666zhaobo666/HoloCubic/源码/My_AIO_Firmware_PIO/src/app/game_2048/README.md

### 2048游戏
APP由`AndyXFuture`编写，原项目链接为`https://github.com/AndyXFuture/HoloCubic-2048-anim`
