666zhaobo666/HoloCubic/源码/My_AIO_Firmware_PIO/src/app/game_snake/README.md

### Snake贪吃蛇
APP由`niyongsheng`编写，项目链接为`https://github.com/niyongsheng/HoloCubic`
