666zhaobo666/HoloCubic/源码/My_AIO_Firmware_PIO/src/app/tomato/README.md

# HoloCubic_AIO_Tomato_Clock_V2.0
透明小电视番茄时钟2.0

本项目基于的代码 https://github.com/ClimbSnail/HoloCubic_AIO
# 原作者
kylefjl

原项目链接：https://github.com/kylefjl/HoloCubic_AIO_TOMATO
# 更新内容
# 界面类

1、增加“专注/休息中.....”运行动画

2、增加毛玻璃效果

# 功能类

1、新增添2个档位：专注45分钟，休息15分钟

2、实现可调节倒计时时间：
  在倒计时进行时，保持前倾增加倒计时开始时间，前倾一下重置当前已设置的倒计时时间
  
# 其他类

1、将倒计时结束时单色闪烁改为RGB渐变闪烁
