666zhaobo666/HoloCubic/AIO_Tool/Holo.png

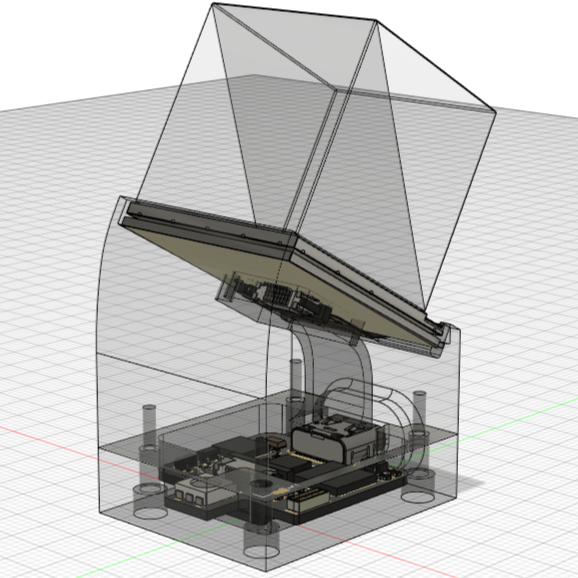
AIO_Tool/Holo.png
