666zhaobo666/HoloCubic/Image/app_bilibili.png

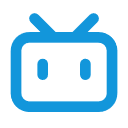
Image/app_bilibili.png
