666zhaobo666/HoloCubic/Image/app_file_manager.png

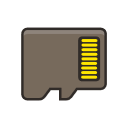
Image/app_file_manager.png
