666zhaobo666/HoloCubic/Image/app_file_maneger_1.png

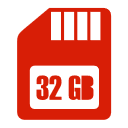
Image/app_file_maneger_1.png
