666zhaobo666/HoloCubic/Image/app_loading.png

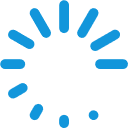
Image/app_loading.png
