666zhaobo666/HoloCubic/Image/app_movie2.png

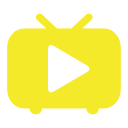
Image/app_movie2.png
