666zhaobo666/HoloCubic/Image/app_movie.png

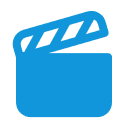
Image/app_movie.png
