666zhaobo666/HoloCubic/Image/app_remote sensor.png

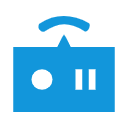
Image/app_remote sensor.png
