666zhaobo666/HoloCubic/Image/app_screen.png

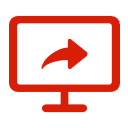
Image/app_screen.png
