666zhaobo666/HoloCubic/Image/app_thought.png

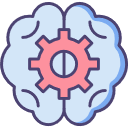
Image/app_thought.png
