666zhaobo666/HoloCubic/Image/app_weather.png

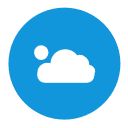
Image/app_weather.png
