666zhaobo666/HoloCubic/Image/bilibili.png

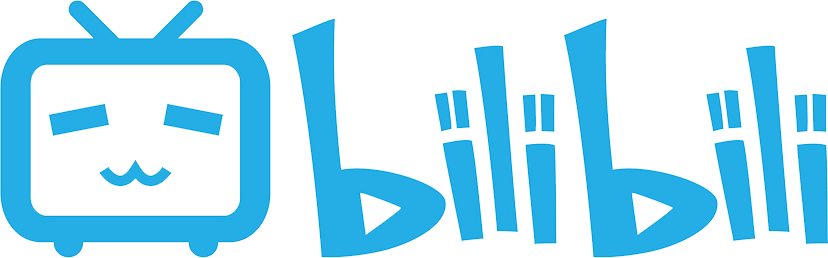
Image/bilibili.png
