666zhaobo666/HoloCubic/Image/butterfly_1.jpg

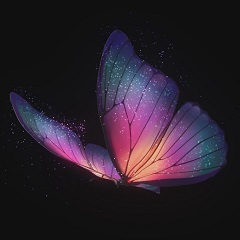
Image/butterfly_1.jpg
