666zhaobo666/HoloCubic/Image/butterfly_2.jpg

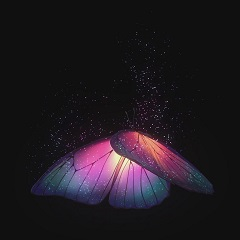
Image/butterfly_2.jpg
