666zhaobo666/HoloCubic/Image/settings.png

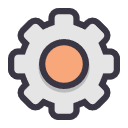
Image/settings.png
