666zhaobo666/HoloCubic/Image/settings_1.png

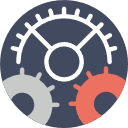
Image/settings_1.png
