666zhaobo666/HoloCubic/Image/thought_anim_2.png

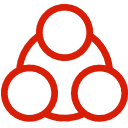
Image/thought_anim_2.png
