666zhaobo666/HoloCubic/Image/thought_anim_3.png

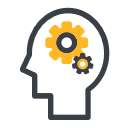
Image/thought_anim_3.png
