666zhaobo666/HoloCubic/lv_simulater_platformio/support/pio_explorer.jpg

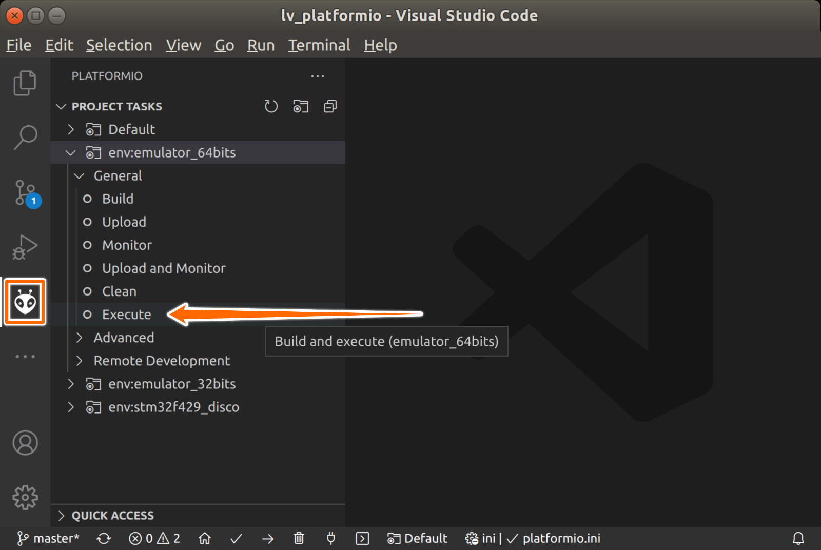
lv_simulater_platformio/support/pio_explorer.jpg
