666zhaobo666/HoloCubic/Metal简版PCB及外壳资料/3D外壳文件/Metal外壳v2.0预览图.png

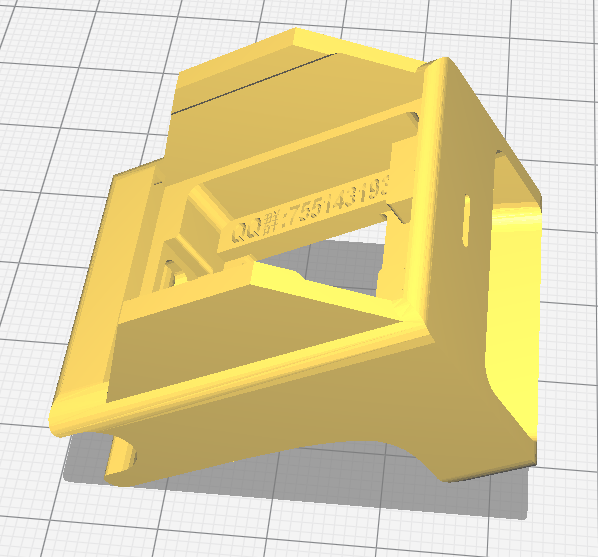
Metal简版PCB及外壳资料/3D外壳文件/Metal外壳v2.0预览图.png
