666zhaobo666/HoloCubic/Metal简版PCB及外壳资料/Metal版本说明_必看.png

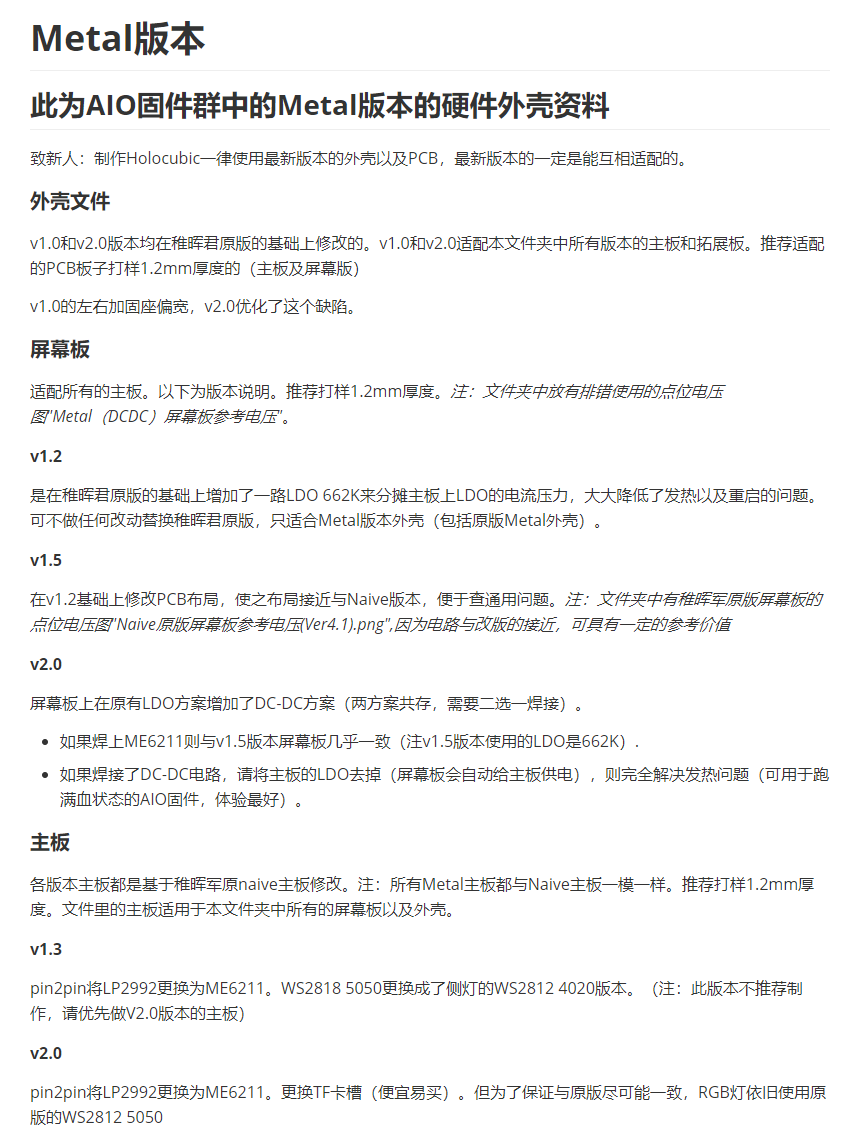
Metal简版PCB及外壳资料/Metal版本说明_必看.png
