666zhaobo666/HoloCubic/Metal简版PCB及外壳资料/主板/主板v1.3/主板v1.3渲染图.png

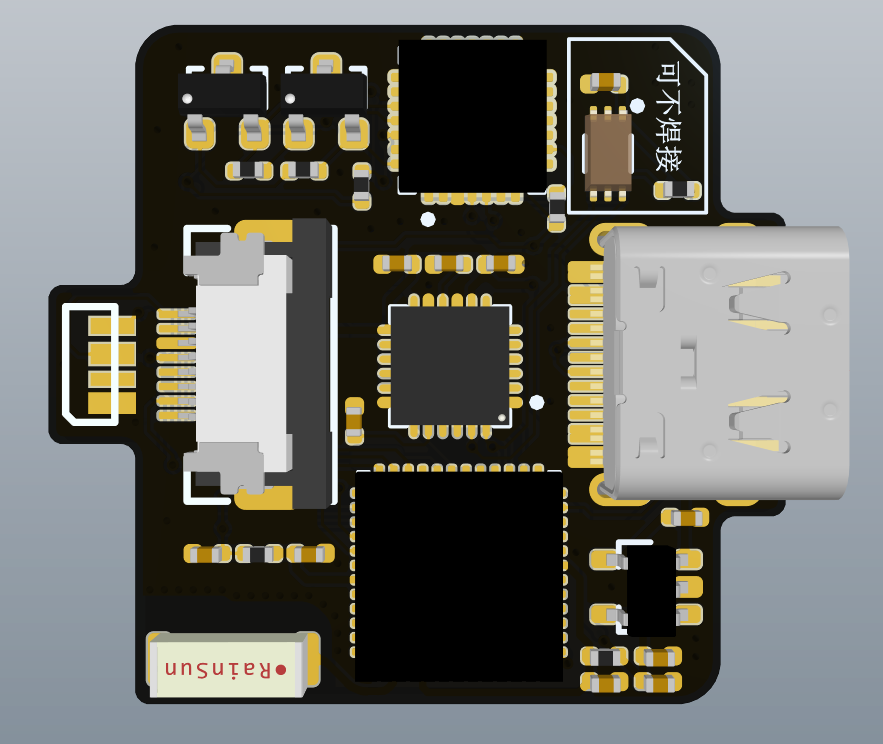
Metal简版PCB及外壳资料/主板/主板v1.3/主板v1.3渲染图.png
