666zhaobo666/HoloCubic/Metal简版PCB及外壳资料/主板/主板v2.0（原版卡槽版）/点位电压图-焊接电阻时.png

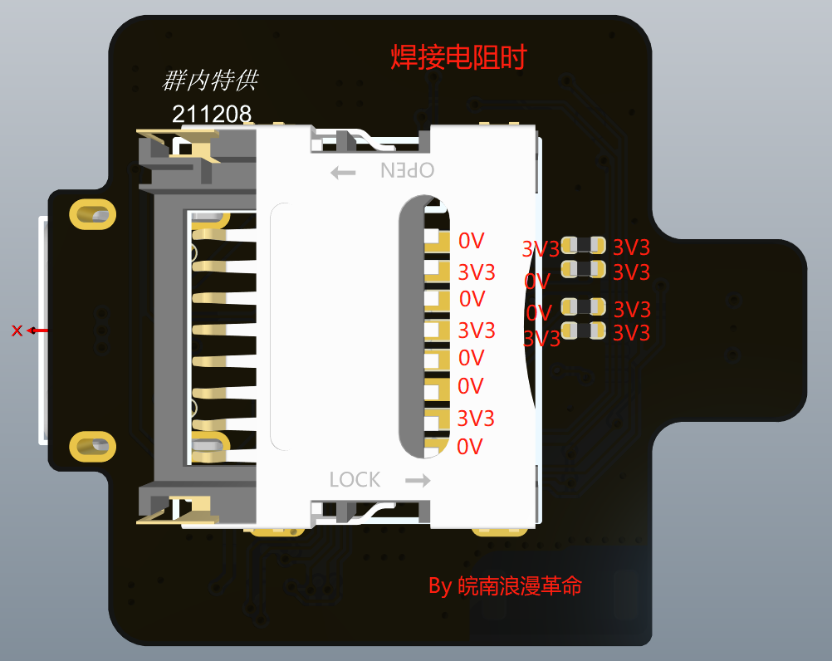
Metal简版PCB及外壳资料/主板/主板v2.0（原版卡槽版）/点位电压图-焊接电阻时.png
