666zhaobo666/HoloCubic/Metal简版PCB及外壳资料/屏幕拓展板/Metal屏幕板v2.0/Metal屏幕板v2.0渲染图.png

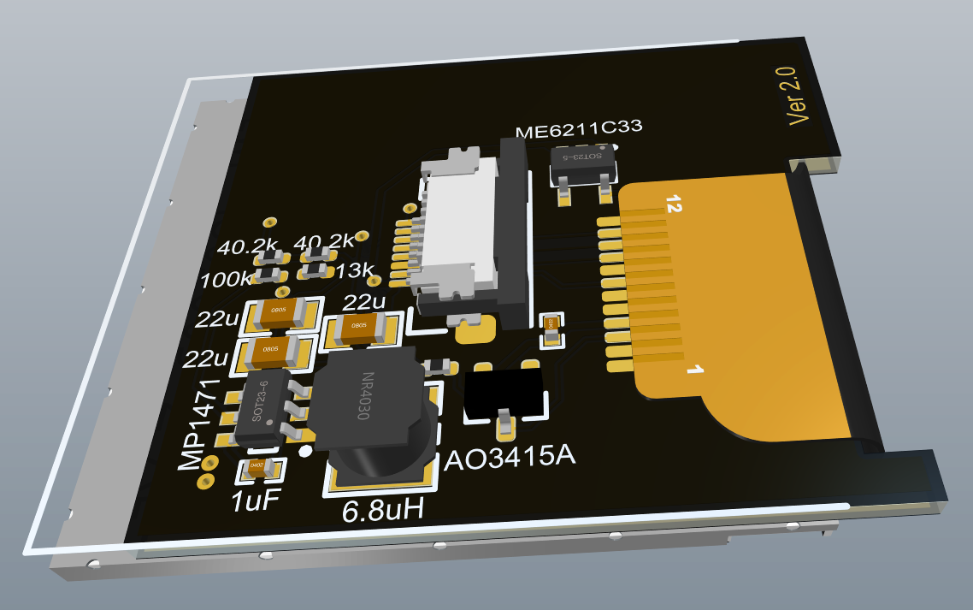
Metal简版PCB及外壳资料/屏幕拓展板/Metal屏幕板v2.0/Metal屏幕板v2.0渲染图.png
