666zhaobo666/HoloCubic/Metal简版PCB及外壳资料/屏幕拓展板/Naive原版屏幕板参考电压(Ver4.1).png

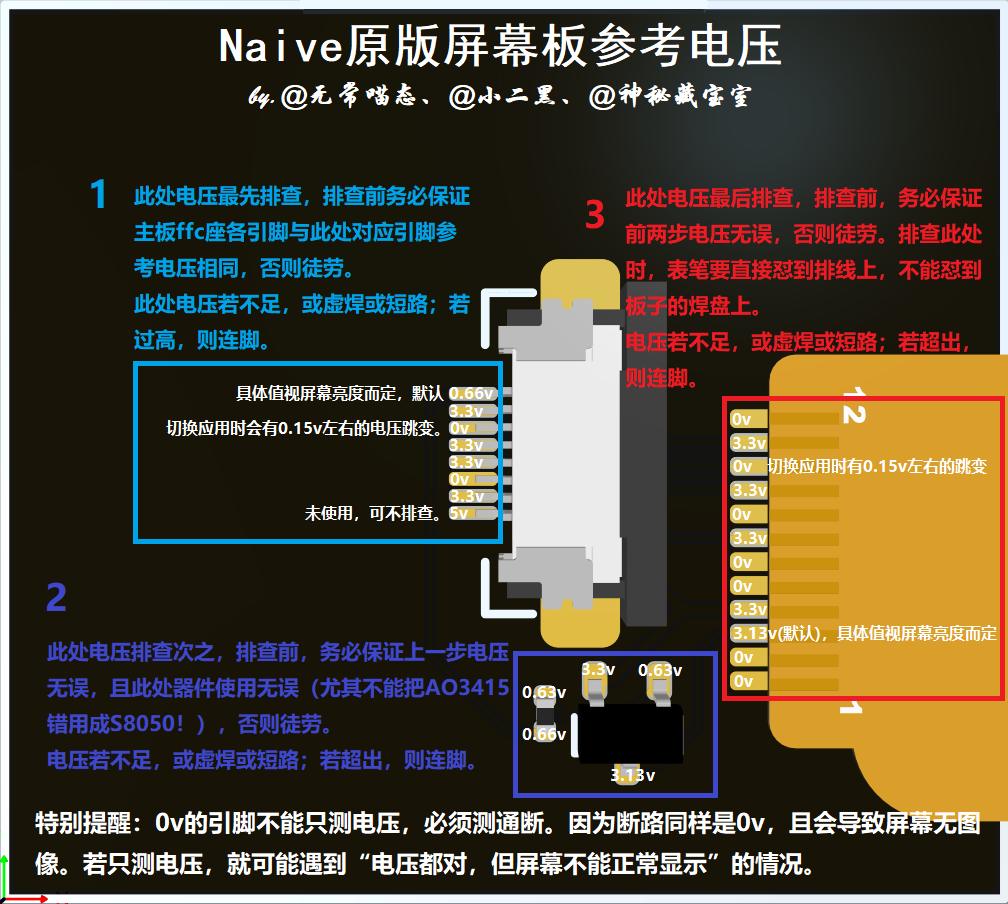
Metal简版PCB及外壳资料/屏幕拓展板/Naive原版屏幕板参考电压(Ver4.1).png
