666zhaobo666/HoloCubic/工具/专用上位机/Cubic上位机v1.4.8/放置内存卡/image/pikaqiu_2.jpg

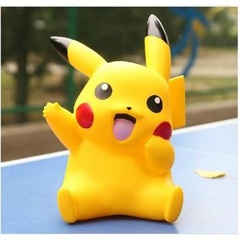
工具/专用上位机/Cubic上位机v1.4.8/放置内存卡/image/pikaqiu_2.jpg
