666zhaobo666/HoloCubic/素材/IMG_20220405_16440978.jpg

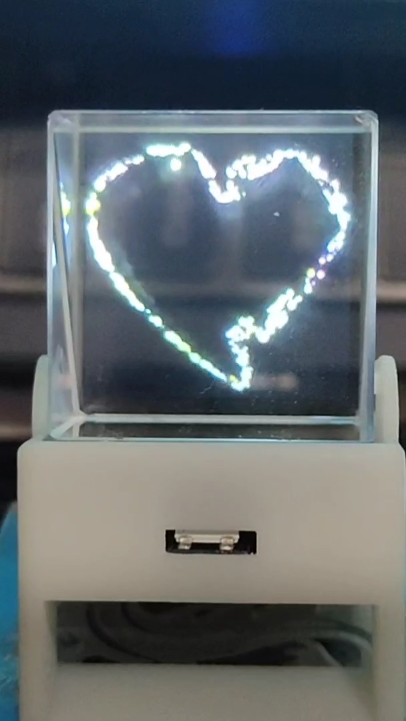
素材/IMG_20220405_16440978.jpg
