666zhaobo666/HoloCubic/素材/太空人动图.gif

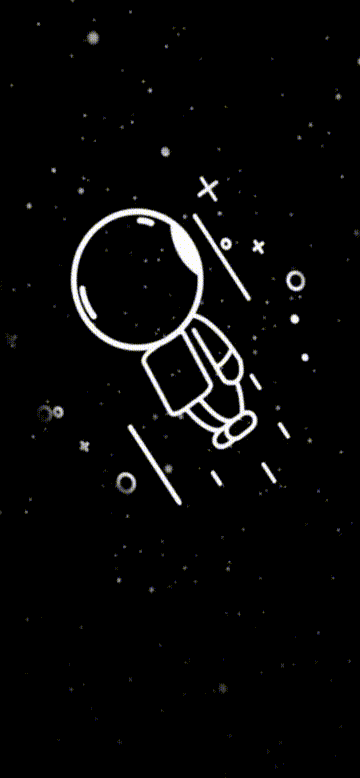
素材/太空人动图.gif
