666zhaobo666/HoloCubic/源码/HoloCubic_AIO_v2.1.8/AIO_Firmware_PIO/src/sys/app_loading.c

#include "app_controller_gui.h"

#if __has_include("lvgl.h")
#include "lvgl.h"
#else
#include "lvgl/lvgl.h"
#endif


#ifndef LV_ATTRIBUTE_MEM_ALIGN
#define LV_ATTRIBUTE_MEM_ALIGN
#endif

#ifndef LV_ATTRIBUTE_IMG_APP_LOADING
#define LV_ATTRIBUTE_IMG_APP_LOADING
#endif


const LV_ATTRIBUTE_MEM_ALIGN LV_ATTRIBUTE_LARGE_CONST LV_ATTRIBUTE_IMG_APP_LOADING uint8_t app_loading_map[] = {
  0x04, 0x02, 0x04, 0xff, 	/*Color of index 0*/
  0xdc, 0x8e, 0x14, 0xff, 	/*Color of index 1*/
  0xd4, 0x96, 0x14, 0xff, 	/*Color of index 2*/
  0xdc, 0x92, 0x14, 0xff, 	/*Color of index 3*/
  0xdc, 0x96, 0x14, 0xff, 	/*Color of index 4*/
  0xff, 0xff, 0xff, 0xff, 	/*Color of index 5*/
  0xff, 0xff, 0xff, 0xff, 	/*Color of index 6*/
  0xff, 0xff, 0xff, 0xff, 	/*Color of index 7*/
  0xff, 0xff, 0xff, 0xff, 	/*Color of index 8*/
  0xff, 0xff, 0xff, 0xff, 	/*Color of index 9*/
  0xff, 0xff, 0xff, 0xff, 	/*Color of index 10*/
  0xff, 0xff, 0xff, 0xff, 	/*Color of index 11*/
  0xff, 0xff, 0xff, 0xff, 	/*Color of index 12*/
  0xff, 0xff, 0xff, 0xff, 	/*Color of index 13*/
  0xff, 0xff, 0xff, 0xff, 	/*Color of index 14*/
  0xff, 0xff, 0xff, 0xff, 	/*Color of index 15*/

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
  0x00, 0x00, 0x00, 0x00, 0x00, 0x04, 0x44, 0x44, 0x44, 0x44, 0x44, 0x44, 0x44, 0x44, 0x44, 0x44, 0x00, 0x00, 0x00, 0x00, 0x00, 0x00, 0x00, 0x00, 0x00, 0x00, 0x00, 0x00, 0x00, 0x00, 0x00, 0x00, 0x00, 0x00, 0x00, 0x00, 0x00, 0x00, 0x00, 0x00, 0x00, 0x00, 0x00, 0x00, 0x00, 0x00, 0x00, 0x00, 0x34, 0x44, 0x44, 0x44, 0x44, 0x44, 0x44, 0x44, 0x44, 0x44, 0x41, 0x00, 0x00, 0x00, 0x00, 0x00, 
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
};

const lv_img_dsc_t app_loading = {
  .header.always_zero = 0,
  .header.w = 128,
  .header.h = 128,
  .data_size = 8256,
  .header.cf = LV_IMG_CF_INDEXED_4BIT,
  .data = app_loading_map,
};
