666zhaobo666/HoloCubic/源码/HoloCubic_AIO_v2.1.8/AIO_Firmware_PIO/src/message.cpp

#include "message.h"
#include <string.h>

MsgHead::MsgHead(MODULE_TYPE from_who, MODULE_TYPE to_who)
{
    m_header_mark = 0x2323;
    m_msg_len = 7;
    m_from_who = from_who;
    m_to_who = to_who;
    m_action_type = AT_UNKNOWN;
}

uint32_t MsgHead::decode(const uint8_t *msg)
{
    if (NULL == msg)
    {
        return 0;
    }
    m_msg_len = msg[2] << 8 + msg[3];
    // m_msg_len = ntohs(msg[2] << 8 + msg[3]);
    m_from_who = (MODULE_TYPE)msg[4];
    m_to_who = (MODULE_TYPE)msg[5];
    m_action_type = (ACTION_TYPE)msg[6];
    return 7;
}

uint32_t MsgHead::encode(uint8_t *msg)
{
    if (NULL == msg)
    {
        return 0;
    }
    msg[0] = 0x23;
    msg[1] = 0x23;
    msg[2] = (uint8_t)(m_msg_len >> 8);
    msg[3] = (uint8_t)(m_msg_len & 0x00FF);
    msg[4] = (uint8_t)m_from_who;
    msg[5] = (uint8_t)m_to_who;
    msg[6] = (uint8_t)m_action_type;
    // uint16_t msg_len = htons(m_msg_len);
    // memcpy((uint8_t *)&msg_len, &msg[4], 2);
    return 7;
}

bool MsgHead::isLegal()
{
    if (m_header_mark != 0x2323)
    {
        return false;
    }
    return true;
}

/********************************************************/
/* SettingsMsg
*********************************************************/

SettingsMsg::SettingsMsg(ACTION_TYPE action_type)
{
    m_msg_head.m_from_who = MODULE_TYPE_CUBIC_SETTINGS;
    m_msg_head.m_to_who = MODULE_TYPE_TOOL_SETTINGS;
    m_msg_head.m_action_type = action_type;
    memset(m_prefs_name, 0, 15);
    memset(m_key, 0, 16);
    m_value_type = VALUE_TYPE_UNKNOWN; // value值的类型
    memset(m_value, 0, 15);
};

uint32_t SettingsMsg::decode(const uint8_t *msg)
{
    if (NULL == msg)
    {
        return 0;
    }
    uint32_t index = m_msg_head.decode(msg);
    // setting数据的后面是以空格隔开的数据段 一般三段
    const char *p_ch = (const char *)msg + index;
    //
    strncpy(m_prefs_name, p_ch, 15);
    for (; *p_ch != 0x00; ++p_ch)
        ;
    p_ch++;

    strncpy(m_key, p_ch, 16);
    for (; *p_ch != 0x00; ++p_ch)
        ;
    p_ch++;

    m_value_type = (VALUE_TYPE)*p_ch;
    p_ch += 2;

    // 解析值 value
    switch (m_value_type)
    {
    case VALUE_TYPE_INT:
    {
        m_value[0] = (unsigned char)(*p_ch);
        p_ch++;
        m_value[1] = (unsigned char)(*p_ch);
        p_ch += 2;
    }
    break;
    case VALUE_TYPE_UCHAR:
    {
        m_value[0] = (unsigned char)(*p_ch);
        p_ch += 2;
    }
    break;
    case VALUE_TYPE_STRING:
    {
        strncpy((char *)m_value, p_ch, 16);
        for (; (*p_ch != ' ') && (*p_ch != '\r'); ++p_ch)
            ;
        p_ch++;
    }
    break;
    default:
        break;
    }

    return index + (p_ch - ((const char *)msg + index));
}

uint32_t SettingsMsg::encode(uint8_t *msg)
{
    // msg最大长度为54字节
    if (NULL == msg)
    {
        return false;
    }
    uint32_t index = m_msg_head.encode(msg);
    strncpy((char *)&msg[index], m_prefs_name, 15);
    index = index + strlen(m_prefs_name) + 1;

    strncpy((char *)&msg[index], m_key, 16);
    index = index + strlen(m_key) + 1;

    m_value_type = (VALUE_TYPE)msg[index];
    index += 2;

    // 解析值 value
    switch (m_value_type)
    {
    case VALUE_TYPE_INT:
    {
        msg[index] = m_value[0];
        index += 1;
        msg[index] = m_value[2];
        index += 2;
    }
    break;
    case VALUE_TYPE_UCHAR:
    {
        msg[index] = m_value[0];
        index += 2;
    }
    break;
    case VALUE_TYPE_STRING:
    {
        strncpy((char *)&msg[index], (char *)m_value, 16);
        index = index + strlen((char *)m_value) + 1;
    }
    break;
    default:
        break;
    }
    m_msg_head.m_msg_len = index;
    m_msg_head.encode(msg);

    return index;
}

bool SettingsMsg::isLegal()
{
    return m_msg_head.isLegal();
}

/********************************************************/
/* FileSystem
*********************************************************/

FileSystem::FileSystem(ACTION_TYPE action_type)
{
    m_msg_head.m_from_who = MODULE_TYPE_CUBIC_FILE_MANAGER;
    m_msg_head.m_to_who = MODULE_TYPE_C_FILE_MANAGER;
    m_msg_head.m_action_type = action_type;
};

uint32_t FileSystem::decode(const uint8_t *msg)
{
    if (NULL == msg)
    {
        return 0;
    }
    uint32_t index = m_msg_head.decode(msg);
    m_msg_head.m_action_type = (ACTION_TYPE)msg[index];
    return index + 1;
}

uint32_t FileSystem::encode(uint8_t *msg)
{
    if (NULL == msg)
    {
        return false;
    }
    uint32_t index = m_msg_head.encode(msg);
    msg[index] = (uint8_t)m_msg_head.m_action_type;
    return index + 1;
}

/********************************************************/
/* DirCreate
*********************************************************/

DirCreate::DirCreate(const char *dir_name)
{
    m_file_system.m_msg_head.m_action_type = AT_DIR_CREATE;
    strncpy(m_dir_path, dir_name, 99);
};

uint32_t DirCreate::decode(const uint8_t *msg)
{
    if (NULL == msg)
    {
        return 0;
    }
    uint32_t index = m_file_system.decode(msg);
    memcpy(m_dir_path, (char *)&msg[index], 99);
    return index + strlen((char *)&msg[index]);
}

uint32_t DirCreate::encode(uint8_t *msg)
{
    if (NULL == msg)
    {
        return false;
    }
    uint32_t index = m_file_system.encode(msg);
    strncpy((char *)&msg[index], m_dir_path, 99);
    return index + strlen(m_dir_path);
}

/********************************************************/
/* DirList
*********************************************************/

DirList::DirList(const char *dir_path, const char *dir_info)
{
    m_file_system.m_msg_head.m_action_type = AT_DIR_LIST;

    if (NULL != dir_path)
    {
        memcpy(m_dir_path, dir_path, 99);
    }
    if (NULL != dir_info)
    {
        memcpy(m_dir_info, dir_info, 400);
    }
};

uint32_t DirList::decode(const uint8_t *msg)
{
    if (NULL == msg)
    {
        return 0;
    }
    uint32_t index = m_file_system.decode(msg);
    memcpy(m_dir_path, (char *)&msg[index], 99);
    memcpy(m_dir_info, (char *)&msg[index + 99], 400);
    m_dir_path[98] = 0;
    m_dir_info[399] = 0;
    return index + 499;
}

uint32_t DirList::encode(uint8_t *msg)
{
    if (NULL == msg)
    {
        return false;
    }
    uint32_t index = m_file_system.encode(msg);
    strncpy((char *)&msg[index], m_dir_path, 99);
    strncpy((char *)&msg[index + 99], m_dir_info, 400);
    m_file_system.m_msg_head.m_msg_len = index + 499;
    m_file_system.encode(msg);
    return index + 499;
}
