666zhaobo666/HoloCubic/源码/HoloCubic_AIO_v2.1.8/AIO_Firmware_PIO/src/message.h

#ifndef FILE_MSG_H
#define FILE_MSG_H

#include "stdint.h"
#include <string.h>

enum MODULE_TYPE : unsigned char
{
    MODULE_TYPE_UNKNOW = 0,
    MODULE_TYPE_CUBIC_FILE_MANAGER,
    MODULE_TYPE_C_FILE_MANAGER,
    MODULE_TYPE_CUBIC_SETTINGS,
    MODULE_TYPE_TOOL_SETTINGS
};

enum ACTION_TYPE : unsigned char
{
    AT_UNKNOWN = 0,
    AT_FREE_STATUS,

    AT_DIR_CREATE,
    AT_DIR_REMOVE,
    AT_DIR_RENAME,
    AT_DIR_LIST,

    AT_FILE_CREATE,
    AT_FILE_WRITE,
    AT_FILE_READ,
    AT_FILE_REMOVE,
    AT_FILE_RENAME,
    AT_FILE_GET_INFO,

    AT_SETTING_SET,
    AT_SETTING_GET,
};

class MsgHead
{
public:
    uint16_t m_header_mark;
    uint16_t m_msg_len;
    MODULE_TYPE m_from_who;
    MODULE_TYPE m_to_who;
    ACTION_TYPE m_action_type;

public:
    MsgHead(MODULE_TYPE from_who = MODULE_TYPE_UNKNOW,
            MODULE_TYPE to_who = MODULE_TYPE_UNKNOW);
    ~MsgHead(){};
    bool isLegal();
    uint32_t decode(const uint8_t *msg);
    uint32_t encode(uint8_t *msg);
};

enum VALUE_TYPE : unsigned char
{
    VALUE_TYPE_UNKNOWN = 0,

    VALUE_TYPE_INT,
    VALUE_TYPE_UCHAR,
    VALUE_TYPE_STRING
};

class SettingsMsg
{
public:
    MsgHead m_msg_head;
    // 以下数据直接使用空格隔开
    char m_prefs_name[15];
    char m_key[16];
    VALUE_TYPE m_value_type;
    unsigned char m_value[15];

public:
    SettingsMsg(ACTION_TYPE action_type = AT_SETTING_SET);
    ~SettingsMsg(){};
    bool isLegal();
    uint32_t decode(const uint8_t *msg);
    uint32_t encode(uint8_t *msg);
};

class FileSystem
{
public:
    MsgHead m_msg_head;

public:
    FileSystem(ACTION_TYPE action_type = AT_FREE_STATUS);
    ~FileSystem(){};
    uint32_t decode(const uint8_t *msg);
    uint32_t encode(uint8_t *msg);
};

class DirCreate
{
public:
    FileSystem m_file_system;
    char m_dir_path[99];

public:
    DirCreate(const char *dir_name = NULL);
    ~DirCreate(){};
    uint32_t decode(const uint8_t *msg);
    uint32_t encode(uint8_t *msg);
};

class DirList
{
public:
    FileSystem m_file_system;
    char m_dir_path[99];
    char m_dir_info[400];   // 用来承载子文件的文件名 多个文件名之间使用\t分隔

public:
    DirList(const char *dir_path = NULL, const char *dir_info = NULL);
    ~DirList(){};
    uint32_t decode(const uint8_t *msg);
    uint32_t encode(uint8_t *msg);
};

#endif
