666zhaobo666/HoloCubic/源码/HoloCubic_AIO_v2.1.8/AIO_Firmware_PIO/src/sys/interface.h

#ifndef INTERFACE_H
#define INTERFACE_H

enum APP_MESSAGE_TYPE
{
    APP_MESSAGE_WIFI_CONN = 0, // 开启连接
    APP_MESSAGE_WIFI_AP,       // 开启AP事件
    APP_MESSAGE_WIFI_ALIVE,    // wifi开关的心跳维持
    APP_MESSAGE_WIFI_DISCONN,  // 连接断开
    APP_MESSAGE_UPDATE_TIME,
    APP_MESSAGE_MQTT_DATA, // MQTT客户端收到消息
    APP_MESSAGE_GET_PARAM, // 获取参数
    APP_MESSAGE_SET_PARAM, // 设置参数
    APP_MESSAGE_READ_CFG,  // 向磁盘读取参数
    APP_MESSAGE_WRITE_CFG, // 向磁盘写入参数

    APP_MESSAGE_NONE
};

enum APP_TYPE
{
    APP_TYPE_REAL_TIME = 0, // 实时应用
    APP_TYPE_BACKGROUND,    // 后台应用

    APP_TYPE_NONE
};

class AppController;
struct ImuAction;

struct APP_OBJ
{
    // 应用程序名称 及title
    const char *app_name;

    // APP的图片存放地址    APP应用图标 128*128
    const void *app_image;

    // 应用程序的其他信息 如作者、版本号等等
    const char *app_info;

    // APP的初始化函数 也可以为空或什么都不做（作用等效于arduino setup()函数）
    int (*app_init)(AppController *sys);

    // APP的主程序函数入口指针
    void (*main_process)(AppController *sys,
                         const ImuAction *act_info);

    // APP的任务的入口指针（一般一分钟内会调用一次）
    void (*background_task)(AppController *sys,
                            const ImuAction *act_info);

    // 退出之前需要处理的回调函数 可为空
    int (*exit_callback)(void *param);

    // 消息处理机制
    void (*message_handle)(const char *from, const char *to,
                           APP_MESSAGE_TYPE type, void *message,
                           void *ext_info);
};

#endif
