666zhaobo666/HoloCubic/AIO_Tool/esptool_v41/flasher_stub/miniz.c

/**************************************************************************
 *
 * Copyright 2013-2014 RAD Game Tools and Valve Software
 * Copyright 2010-2014 Rich Geldreich and Tenacious Software LLC
 * All Rights Reserved.
 *
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
 **************************************************************************/

#include  "miniz.h"

typedef unsigned char mz_validate_uint16[sizeof(mz_uint16) == 2 ? 1 : -1];
typedef unsigned char mz_validate_uint32[sizeof(mz_uint32) == 4 ? 1 : -1];
typedef unsigned char mz_validate_uint64[sizeof(mz_uint64) == 8 ? 1 : -1];

#ifdef __cplusplus
extern "C" {
#endif

/* ------------------- zlib-style API's */

mz_ulong mz_adler32(mz_ulong adler, const unsigned char *ptr, size_t buf_len)
{
    mz_uint32 i, s1 = (mz_uint32)(adler & 0xffff), s2 = (mz_uint32)(adler >> 16);
    size_t block_len = buf_len % 5552;
    if (!ptr)
        return MZ_ADLER32_INIT;
    while (buf_len)
    {
        for (i = 0; i + 7 < block_len; i += 8, ptr += 8)
        {
            s1 += ptr[0], s2 += s1;
            s1 += ptr[1], s2 += s1;
            s1 += ptr[2], s2 += s1;
            s1 += ptr[3], s2 += s1;
            s1 += ptr[4], s2 += s1;
            s1 += ptr[5], s2 += s1;
            s1 += ptr[6], s2 += s1;
            s1 += ptr[7], s2 += s1;
        }
        for (; i < block_len; ++i)
            s1 += *ptr++, s2 += s1;
        s1 %= 65521U, s2 %= 65521U;
        buf_len -= block_len;
        block_len = 5552;
    }
    return (s2 << 16) + s1;
}

/* Karl Malbrain's compact CRC-32. See "A compact CCITT crc16 and crc32 C implementation that balances processor cache usage against speed": http://www.geocities.com/malbrain/ */
#if 0
    mz_ulong mz_crc32(mz_ulong crc, const mz_uint8 *ptr, size_t buf_len)
    {
        static const mz_uint32 s_crc32[16] = { 0, 0x1db71064, 0x3b6e20c8, 0x26d930ac, 0x76dc4190, 0x6b6b51f4, 0x4db26158, 0x5005713c,
                                               0xedb88320, 0xf00f9344, 0xd6d6a3e8, 0xcb61b38c, 0x9b64c2b0, 0x86d3d2d4, 0xa00ae278, 0xbdbdf21c };
        mz_uint32 crcu32 = (mz_uint32)crc;
        if (!ptr)
            return MZ_CRC32_INIT;
        crcu32 = ~crcu32;
        while (buf_len--)
        {
            mz_uint8 b = *ptr++;
            crcu32 = (crcu32 >> 4) ^ s_crc32[(crcu32 & 0xF) ^ (b & 0xF)];
            crcu32 = (crcu32 >> 4) ^ s_crc32[(crcu32 & 0xF) ^ (b >> 4)];
        }
        return ~crcu32;
    }
#else
/* Faster, but larger CPU cache footprint.
 */
mz_ulong mz_crc32(mz_ulong crc, const mz_uint8 *ptr, size_t buf_len)
{
    static const mz_uint32 s_crc_table[256] =
        {
          0x00000000, 0x77073096, 0xEE0E612C, 0x990951BA, 0x076DC419, 0x706AF48F, 0xE963A535,
          0x9E6495A3, 0x0EDB8832, 0x79DCB8A4, 0xE0D5E91E, 0x97D2D988, 0x09B64C2B, 0x7EB17CBD,
          0xE7B82D07, 0x90BF1D91, 0x1DB71064, 0x6AB020F2, 0xF3B97148, 0x84BE41DE, 0x1ADAD47D,
          0x6DDDE4EB, 0xF4D4B551, 0x83D385C7, 0x136C9856, 0x646BA8C0, 0xFD62F97A, 0x8A65C9EC,
          0x14015C4F, 0x63066CD9, 0xFA0F3D63, 0x8D080DF5, 0x3B6E20C8, 0x4C69105E, 0xD56041E4,
          0xA2677172, 0x3C03E4D1, 0x4B04D447, 0xD20D85FD, 0xA50AB56B, 0x35B5A8FA, 0x42B2986C,
          0xDBBBC9D6, 0xACBCF940, 0x32D86CE3, 0x45DF5C75, 0xDCD60DCF, 0xABD13D59, 0x26D930AC,
          0x51DE003A, 0xC8D75180, 0xBFD06116, 0x21B4F4B5, 0x56B3C423, 0xCFBA9599, 0xB8BDA50F,
          0x2802B89E, 0x5F058808, 0xC60CD9B2, 0xB10BE924, 0x2F6F7C87, 0x58684C11, 0xC1611DAB,
          0xB6662D3D, 0x76DC4190, 0x01DB7106, 0x98D220BC, 0xEFD5102A, 0x71B18589, 0x06B6B51F,
          0x9FBFE4A5, 0xE8B8D433, 0x7807C9A2, 0x0F00F934, 0x9609A88E, 0xE10E9818, 0x7F6A0DBB,
          0x086D3D2D, 0x91646C97, 0xE6635C01, 0x6B6B51F4, 0x1C6C6162, 0x856530D8, 0xF262004E,
          0x6C0695ED, 0x1B01A57B, 0x8208F4C1, 0xF50FC457, 0x65B0D9C6, 0x12B7E950, 0x8BBEB8EA,
          0xFCB9887C, 0x62DD1DDF, 0x15DA2D49, 0x8CD37CF3, 0xFBD44C65, 0x4DB26158, 0x3AB551CE,
          0xA3BC0074, 0xD4BB30E2, 0x4ADFA541, 0x3DD895D7, 0xA4D1C46D, 0xD3D6F4FB, 0x4369E96A,
          0x346ED9FC, 0xAD678846, 0xDA60B8D0, 0x44042D73, 0x33031DE5, 0xAA0A4C5F, 0xDD0D7CC9,
          0x5005713C, 0x270241AA, 0xBE0B1010, 0xC90C2086, 0x5768B525, 0x206F85B3, 0xB966D409,
          0xCE61E49F, 0x5EDEF90E, 0x29D9C998, 0xB0D09822, 0xC7D7A8B4, 0x59B33D17, 0x2EB40D81,
          0xB7BD5C3B, 0xC0BA6CAD, 0xEDB88320, 0x9ABFB3B6, 0x03B6E20C, 0x74B1D29A, 0xEAD54739,
          0x9DD277AF, 0x04DB2615, 0x73DC1683, 0xE3630B12, 0x94643B84, 0x0D6D6A3E, 0x7A6A5AA8,
          0xE40ECF0B, 0x9309FF9D, 0x0A00AE27, 0x7D079EB1, 0xF00F9344, 0x8708A3D2, 0x1E01F268,
          0x6906C2FE, 0xF762575D, 0x806567CB, 0x196C3671, 0x6E6B06E7, 0xFED41B76, 0x89D32BE0,
          0x10DA7A5A, 0x67DD4ACC, 0xF9B9DF6F, 0x8EBEEFF9, 0x17B7BE43, 0x60B08ED5, 0xD6D6A3E8,
          0xA1D1937E, 0x38D8C2C4, 0x4FDFF252, 0xD1BB67F1, 0xA6BC5767, 0x3FB506DD, 0x48B2364B,
          0xD80D2BDA, 0xAF0A1B4C, 0x36034AF6, 0x41047A60, 0xDF60EFC3, 0xA867DF55, 0x316E8EEF,
          0x4669BE79, 0xCB61B38C, 0xBC66831A, 0x256FD2A0, 0x5268E236, 0xCC0C7795, 0xBB0B4703,
          0x220216B9, 0x5505262F, 0xC5BA3BBE, 0xB2BD0B28, 0x2BB45A92, 0x5CB36A04, 0xC2D7FFA7,
          0xB5D0CF31, 0x2CD99E8B, 0x5BDEAE1D, 0x9B64C2B0, 0xEC63F226, 0x756AA39C, 0x026D930A,
          0x9C0906A9, 0xEB0E363F, 0x72076785, 0x05005713, 0x95BF4A82, 0xE2B87A14, 0x7BB12BAE,
          0x0CB61B38, 0x92D28E9B, 0xE5D5BE0D, 0x7CDCEFB7, 0x0BDBDF21, 0x86D3D2D4, 0xF1D4E242,
          0x68DDB3F8, 0x1FDA836E, 0x81BE16CD, 0xF6B9265B, 0x6FB077E1, 0x18B74777, 0x88085AE6,
          0xFF0F6A70, 0x66063BCA, 0x11010B5C, 0x8F659EFF, 0xF862AE69, 0x616BFFD3, 0x166CCF45,
          0xA00AE278, 0xD70DD2EE, 0x4E048354, 0x3903B3C2, 0xA7672661, 0xD06016F7, 0x4969474D,
          0x3E6E77DB, 0xAED16A4A, 0xD9D65ADC, 0x40DF0B66, 0x37D83BF0, 0xA9BCAE53, 0xDEBB9EC5,
          0x47B2CF7F, 0x30B5FFE9, 0xBDBDF21C, 0xCABAC28A, 0x53B39330, 0x24B4A3A6, 0xBAD03605,
          0xCDD70693, 0x54DE5729, 0x23D967BF, 0xB3667A2E, 0xC4614AB8, 0x5D681B02, 0x2A6F2B94,
          0xB40BBE37, 0xC30C8EA1, 0x5A05DF1B, 0x2D02EF8D
        };

    mz_uint32 crc32 = (mz_uint32)crc ^ 0xFFFFFFFF;
    const mz_uint8 *pByte_buf = (const mz_uint8 *)ptr;

    while (buf_len >= 4)
    {
        crc32 = (crc32 >> 8) ^ s_crc_table[(crc32 ^ pByte_buf[0]) & 0xFF];
        crc32 = (crc32 >> 8) ^ s_crc_table[(crc32 ^ pByte_buf[1]) & 0xFF];
        crc32 = (crc32 >> 8) ^ s_crc_table[(crc32 ^ pByte_buf[2]) & 0xFF];
        crc32 = (crc32 >> 8) ^ s_crc_table[(crc32 ^ pByte_buf[3]) & 0xFF];
        pByte_buf += 4;
        buf_len -= 4;
    }

    while (buf_len)
    {
        crc32 = (crc32 >> 8) ^ s_crc_table[(crc32 ^ pByte_buf[0]) & 0xFF];
        ++pByte_buf;
        --buf_len;
    }

    return ~crc32;
}
#endif

void mz_free(void *p)
{
    MZ_FREE(p);
}

void *miniz_def_alloc_func(void *opaque, size_t items, size_t size)
{
    (void)opaque, (void)items, (void)size;
    return MZ_MALLOC(items * size);
}
void miniz_def_free_func(void *opaque, void *address)
{
    (void)opaque, (void)address;
    MZ_FREE(address);
}
void *miniz_def_realloc_func(void *opaque, void *address, size_t items, size_t size)
{
    (void)opaque, (void)address, (void)items, (void)size;
    return MZ_REALLOC(address, items * size);
}

const char *mz_version(void)
{
    return MZ_VERSION;
}

#ifndef MINIZ_NO_ZLIB_APIS

int mz_deflateInit(mz_streamp pStream, int level)
{
    return mz_deflateInit2(pStream, level, MZ_DEFLATED, MZ_DEFAULT_WINDOW_BITS, 9, MZ_DEFAULT_STRATEGY);
}

int mz_deflateInit2(mz_streamp pStream, int level, int method, int window_bits, int mem_level, int strategy)
{
    tdefl_compressor *pComp;
    mz_uint comp_flags = TDEFL_COMPUTE_ADLER32 | tdefl_create_comp_flags_from_zip_params(level, window_bits, strategy);

    if (!pStream)
        return MZ_STREAM_ERROR;
    if ((method != MZ_DEFLATED) || ((mem_level < 1) || (mem_level > 9)) || ((window_bits != MZ_DEFAULT_WINDOW_BITS) && (-window_bits != MZ_DEFAULT_WINDOW_BITS)))
        return MZ_PARAM_ERROR;

    pStream->data_type = 0;
    pStream->adler = MZ_ADLER32_INIT;
    pStream->msg = NULL;
    pStream->reserved = 0;
    pStream->total_in = 0;
    pStream->total_out = 0;
    if (!pStream->zalloc)
        pStream->zalloc = miniz_def_alloc_func;
    if (!pStream->zfree)
        pStream->zfree = miniz_def_free_func;

    pComp = (tdefl_compressor *)pStream->zalloc(pStream->opaque, 1, sizeof(tdefl_compressor));
    if (!pComp)
        return MZ_MEM_ERROR;

    pStream->state = (struct mz_internal_state *)pComp;

    if (tdefl_init(pComp, NULL, NULL, comp_flags) != TDEFL_STATUS_OKAY)
    {
        mz_deflateEnd(pStream);
        return MZ_PARAM_ERROR;
    }

    return MZ_OK;
}

int mz_deflateReset(mz_streamp pStream)
{
    if ((!pStream) || (!pStream->state) || (!pStream->zalloc) || (!pStream->zfree))
        return MZ_STREAM_ERROR;
    pStream->total_in = pStream->total_out = 0;
    tdefl_init((tdefl_compressor *)pStream->state, NULL, NULL, ((tdefl_compressor *)pStream->state)->m_flags);
    return MZ_OK;
}

int mz_deflate(mz_streamp pStream, int flush)
{
    size_t in_bytes, out_bytes;
    mz_ulong orig_total_in, orig_total_out;
    int mz_status = MZ_OK;

    if ((!pStream) || (!pStream->state) || (flush < 0) || (flush > MZ_FINISH) || (!pStream->next_out))
        return MZ_STREAM_ERROR;
    if (!pStream->avail_out)
        return MZ_BUF_ERROR;

    if (flush == MZ_PARTIAL_FLUSH)
        flush = MZ_SYNC_FLUSH;

    if (((tdefl_compressor *)pStream->state)->m_prev_return_status == TDEFL_STATUS_DONE)
        return (flush == MZ_FINISH) ? MZ_STREAM_END : MZ_BUF_ERROR;

    orig_total_in = pStream->total_in;
    orig_total_out = pStream->total_out;
    for (;;)
    {
        tdefl_status defl_status;
        in_bytes = pStream->avail_in;
        out_bytes = pStream->avail_out;

        defl_status = tdefl_compress((tdefl_compressor *)pStream->state, pStream->next_in, &in_bytes, pStream->next_out, &out_bytes, (tdefl_flush)flush);
        pStream->next_in += (mz_uint)in_bytes;
        pStream->avail_in -= (mz_uint)in_bytes;
        pStream->total_in += (mz_uint)in_bytes;
        pStream->adler = tdefl_get_adler32((tdefl_compressor *)pStream->state);

        pStream->next_out += (mz_uint)out_bytes;
        pStream->avail_out -= (mz_uint)out_bytes;
        pStream->total_out += (mz_uint)out_bytes;

        if (defl_status < 0)
        {
            mz_status = MZ_STREAM_ERROR;
            break;
        }
        else if (defl_status == TDEFL_STATUS_DONE)
        {
            mz_status = MZ_STREAM_END;
            break;
        }
        else if (!pStream->avail_out)
            break;
        else if ((!pStream->avail_in) && (flush != MZ_FINISH))
        {
            if ((flush) || (pStream->total_in != orig_total_in) || (pStream->total_out != orig_total_out))
                break;
            return MZ_BUF_ERROR; /* Can't make forward progress without some input.
 */
        }
    }
    return mz_status;
}

int mz_deflateEnd(mz_streamp pStream)
{
    if (!pStream)
        return MZ_STREAM_ERROR;
    if (pStream->state)
    {
        pStream->zfree(pStream->opaque, pStream->state);
        pStream->state = NULL;
    }
    return MZ_OK;
}

mz_ulong mz_deflateBound(mz_streamp pStream, mz_ulong source_len)
{
    (void)pStream;
    /* This is really over conservative. (And lame, but it's actually pretty tricky to compute a true upper bound given the way tdefl's blocking works.) */
    return MZ_MAX(128 + (source_len * 110) / 100, 128 + source_len + ((source_len / (31 * 1024)) + 1) * 5);
}

int mz_compress2(unsigned char *pDest, mz_ulong *pDest_len, const unsigned char *pSource, mz_ulong source_len, int level)
{
    int status;
    mz_stream stream;
    memset(&stream, 0, sizeof(stream));

    /* In case mz_ulong is 64-bits (argh I hate longs). */
    if ((source_len | *pDest_len) > 0xFFFFFFFFU)
        return MZ_PARAM_ERROR;

    stream.next_in = pSource;
    stream.avail_in = (mz_uint32)source_len;
    stream.next_out = pDest;
    stream.avail_out = (mz_uint32)*pDest_len;

    status = mz_deflateInit(&stream, level);
    if (status != MZ_OK)
        return status;

    status = mz_deflate(&stream, MZ_FINISH);
    if (status != MZ_STREAM_END)
    {
        mz_deflateEnd(&stream);
        return (status == MZ_OK) ? MZ_BUF_ERROR : status;
    }

    *pDest_len = stream.total_out;
    return mz_deflateEnd(&stream);
}

int mz_compress(unsigned char *pDest, mz_ulong *pDest_len, const unsigned char *pSource, mz_ulong source_len)
{
    return mz_compress2(pDest, pDest_len, pSource, source_len, MZ_DEFAULT_COMPRESSION);
}

mz_ulong mz_compressBound(mz_ulong source_len)
{
    return mz_deflateBound(NULL, source_len);
}

typedef struct
{
    tinfl_decompressor m_decomp;
    mz_uint m_dict_ofs, m_dict_avail, m_first_call, m_has_flushed;
    int m_window_bits;
    mz_uint8 m_dict[TINFL_LZ_DICT_SIZE];
    tinfl_status m_last_status;
} inflate_state;

int mz_inflateInit2(mz_streamp pStream, int window_bits)
{
    inflate_state *pDecomp;
    if (!pStream)
        return MZ_STREAM_ERROR;
    if ((window_bits != MZ_DEFAULT_WINDOW_BITS) && (-window_bits != MZ_DEFAULT_WINDOW_BITS))
        return MZ_PARAM_ERROR;

    pStream->data_type = 0;
    pStream->adler = 0;
    pStream->msg = NULL;
    pStream->total_in = 0;
    pStream->total_out = 0;
    pStream->reserved = 0;
    if (!pStream->zalloc)
        pStream->zalloc = miniz_def_alloc_func;
    if (!pStream->zfree)
        pStream->zfree = miniz_def_free_func;

    pDecomp = (inflate_state *)pStream->zalloc(pStream->opaque, 1, sizeof(inflate_state));
    if (!pDecomp)
        return MZ_MEM_ERROR;

    pStream->state = (struct mz_internal_state *)pDecomp;

    tinfl_init(&pDecomp->m_decomp);
    pDecomp->m_dict_ofs = 0;
    pDecomp->m_dict_avail = 0;
    pDecomp->m_last_status = TINFL_STATUS_NEEDS_MORE_INPUT;
    pDecomp->m_first_call = 1;
    pDecomp->m_has_flushed = 0;
    pDecomp->m_window_bits = window_bits;

    return MZ_OK;
}

int mz_inflateInit(mz_streamp pStream)
{
    return mz_inflateInit2(pStream, MZ_DEFAULT_WINDOW_BITS);
}

int mz_inflateReset(mz_streamp pStream)
{
    inflate_state *pDecomp;
    if (!pStream)
        return MZ_STREAM_ERROR;

    pStream->data_type = 0;
    pStream->adler = 0;
    pStream->msg = NULL;
    pStream->total_in = 0;
    pStream->total_out = 0;
    pStream->reserved = 0;

    pDecomp = (inflate_state *)pStream->state;

    tinfl_init(&pDecomp->m_decomp);
    pDecomp->m_dict_ofs = 0;
    pDecomp->m_dict_avail = 0;
    pDecomp->m_last_status = TINFL_STATUS_NEEDS_MORE_INPUT;
    pDecomp->m_first_call = 1;
    pDecomp->m_has_flushed = 0;
    /* pDecomp->m_window_bits = window_bits */;

    return MZ_OK;
}

int mz_inflate(mz_streamp pStream, int flush)
{
    inflate_state *pState;
    mz_uint n, first_call, decomp_flags = TINFL_FLAG_COMPUTE_ADLER32;
    size_t in_bytes, out_bytes, orig_avail_in;
    tinfl_status status;

    if ((!pStream) || (!pStream->state))
        return MZ_STREAM_ERROR;
    if (flush == MZ_PARTIAL_FLUSH)
        flush = MZ_SYNC_FLUSH;
    if ((flush) && (flush != MZ_SYNC_FLUSH) && (flush != MZ_FINISH))
        return MZ_STREAM_ERROR;

    pState = (inflate_state *)pStream->state;
    if (pState->m_window_bits > 0)
        decomp_flags |= TINFL_FLAG_PARSE_ZLIB_HEADER;
    orig_avail_in = pStream->avail_in;

    first_call = pState->m_first_call;
    pState->m_first_call = 0;
    if (pState->m_last_status < 0)
        return MZ_DATA_ERROR;

    if (pState->m_has_flushed && (flush != MZ_FINISH))
        return MZ_STREAM_ERROR;
    pState->m_has_flushed |= (flush == MZ_FINISH);

    if ((flush == MZ_FINISH) && (first_call))
    {
        /* MZ_FINISH on the first call implies that the input and output buffers are large enough to hold the entire compressed/decompressed file. */
        decomp_flags |= TINFL_FLAG_USING_NON_WRAPPING_OUTPUT_BUF;
        in_bytes = pStream->avail_in;
        out_bytes = pStream->avail_out;
        status = tinfl_decompress(&pState->m_decomp, pStream->next_in, &in_bytes, pStream->next_out, pStream->next_out, &out_bytes, decomp_flags);
        pState->m_last_status = status;
        pStream->next_in += (mz_uint)in_bytes;
        pStream->avail_in -= (mz_uint)in_bytes;
        pStream->total_in += (mz_uint)in_bytes;
        pStream->adler = tinfl_get_adler32(&pState->m_decomp);
        pStream->next_out += (mz_uint)out_bytes;
        pStream->avail_out -= (mz_uint)out_bytes;
        pStream->total_out += (mz_uint)out_bytes;

        if (status < 0)
            return MZ_DATA_ERROR;
        else if (status != TINFL_STATUS_DONE)
        {
            pState->m_last_status = TINFL_STATUS_FAILED;
            return MZ_BUF_ERROR;
        }
        return MZ_STREAM_END;
    }
    /* flush != MZ_FINISH then we must assume there's more input. */
    if (flush != MZ_FINISH)
        decomp_flags |= TINFL_FLAG_HAS_MORE_INPUT;

    if (pState->m_dict_avail)
    {
        n = MZ_MIN(pState->m_dict_avail, pStream->avail_out);
        memcpy(pStream->next_out, pState->m_dict + pState->m_dict_ofs, n);
        pStream->next_out += n;
        pStream->avail_out -= n;
        pStream->total_out += n;
        pState->m_dict_avail -= n;
        pState->m_dict_ofs = (pState->m_dict_ofs + n) & (TINFL_LZ_DICT_SIZE - 1);
        return ((pState->m_last_status == TINFL_STATUS_DONE) && (!pState->m_dict_avail)) ? MZ_STREAM_END : MZ_OK;
    }

    for (;;)
    {
        in_bytes = pStream->avail_in;
        out_bytes = TINFL_LZ_DICT_SIZE - pState->m_dict_ofs;

        status = tinfl_decompress(&pState->m_decomp, pStream->next_in, &in_bytes, pState->m_dict, pState->m_dict + pState->m_dict_ofs, &out_bytes, decomp_flags);
        pState->m_last_status = status;

        pStream->next_in += (mz_uint)in_bytes;
        pStream->avail_in -= (mz_uint)in_bytes;
        pStream->total_in += (mz_uint)in_bytes;
        pStream->adler = tinfl_get_adler32(&pState->m_decomp);

        pState->m_dict_avail = (mz_uint)out_bytes;

        n = MZ_MIN(pState->m_dict_avail, pStream->avail_out);
        memcpy(pStream->next_out, pState->m_dict + pState->m_dict_ofs, n);
        pStream->next_out += n;
        pStream->avail_out -= n;
        pStream->total_out += n;
        pState->m_dict_avail -= n;
        pState->m_dict_ofs = (pState->m_dict_ofs + n) & (TINFL_LZ_DICT_SIZE - 1);

        if (status < 0)
            return MZ_DATA_ERROR; /* Stream is corrupted (there could be some uncompressed data left in the output dictionary - oh well). */
        else if ((status == TINFL_STATUS_NEEDS_MORE_INPUT) && (!orig_avail_in))
            return MZ_BUF_ERROR; /* Signal caller that we can't make forward progress without supplying more input or by setting flush to MZ_FINISH. */
        else if (flush == MZ_FINISH)
        {
            /* The output buffer MUST be large to hold the remaining uncompressed data when flush==MZ_FINISH. */
            if (status == TINFL_STATUS_DONE)
                return pState->m_dict_avail ? MZ_BUF_ERROR : MZ_STREAM_END;
            /* status here must be TINFL_STATUS_HAS_MORE_OUTPUT, which means there's at least 1 more byte on the way. If there's no more room left in the output buffer then something is wrong. */
            else if (!pStream->avail_out)
                return MZ_BUF_ERROR;
        }
        else if ((status == TINFL_STATUS_DONE) || (!pStream->avail_in) || (!pStream->avail_out) || (pState->m_dict_avail))
            break;
    }

    return ((status == TINFL_STATUS_DONE) && (!pState->m_dict_avail)) ? MZ_STREAM_END : MZ_OK;
}

int mz_inflateEnd(mz_streamp pStream)
{
    if (!pStream)
        return MZ_STREAM_ERROR;
    if (pStream->state)
    {
        pStream->zfree(pStream->opaque, pStream->state);
        pStream->state = NULL;
    }
    return MZ_OK;
}

int mz_uncompress(unsigned char *pDest, mz_ulong *pDest_len, const unsigned char *pSource, mz_ulong source_len)
{
    mz_stream stream;
    int status;
    memset(&stream, 0, sizeof(stream));

    /* In case mz_ulong is 64-bits (argh I hate longs). */
    if ((source_len | *pDest_len) > 0xFFFFFFFFU)
        return MZ_PARAM_ERROR;

    stream.next_in = pSource;
    stream.avail_in = (mz_uint32)source_len;
    stream.next_out = pDest;
    stream.avail_out = (mz_uint32)*pDest_len;

    status = mz_inflateInit(&stream);
    if (status != MZ_OK)
        return status;

    status = mz_inflate(&stream, MZ_FINISH);
    if (status != MZ_STREAM_END)
    {
        mz_inflateEnd(&stream);
        return ((status == MZ_BUF_ERROR) && (!stream.avail_in)) ? MZ_DATA_ERROR : status;
    }
    *pDest_len = stream.total_out;

    return mz_inflateEnd(&stream);
}

const char *mz_error(int err)
{
    static struct
    {
        int m_err;
        const char *m_pDesc;
    } s_error_descs[] =
        {
          { MZ_OK, "" }, { MZ_STREAM_END, "stream end" }, { MZ_NEED_DICT, "need dictionary" }, { MZ_ERRNO, "file error" }, { MZ_STREAM_ERROR, "stream error" }, { MZ_DATA_ERROR, "data error" }, { MZ_MEM_ERROR, "out of memory" }, { MZ_BUF_ERROR, "buf error" }, { MZ_VERSION_ERROR, "version error" }, { MZ_PARAM_ERROR, "parameter error" }
        };
    mz_uint i;
    for (i = 0; i < sizeof(s_error_descs) / sizeof(s_error_descs[0]); ++i)
        if (s_error_descs[i].m_err == err)
            return s_error_descs[i].m_pDesc;
    return NULL;
}

#endif /*MINIZ_NO_ZLIB_APIS */

#ifdef __cplusplus
}
#endif

/*
  This is free and unencumbered software released into the public domain.

  Anyone is free to copy, modify, publish, use, compile, sell, or
  distribute this software, either in source code form or as a compiled
  binary, for any purpose, commercial or non-commercial, and by any
  means.

  In jurisdictions that recognize copyright laws, the author or authors
  of this software dedicate any and all copyright interest in the
  software to the public domain. We make this dedication for the benefit
  of the public at large and to the detriment of our heirs and
  successors. We intend this dedication to be an overt act of
  relinquishment in perpetuity of all present and future rights to this
  software under copyright law.

  THE SOFTWARE IS PROVIDED "AS IS", WITHOUT WARRANTY OF ANY KIND,
  EXPRESS OR IMPLIED, INCLUDING BUT NOT LIMITED TO THE WARRANTIES OF
  MERCHANTABILITY, FITNESS FOR A PARTICULAR PURPOSE AND NONINFRINGEMENT.
  IN NO EVENT SHALL THE AUTHORS BE LIABLE FOR ANY CLAIM, DAMAGES OR
  OTHER LIABILITY, WHETHER IN AN ACTION OF CONTRACT, TORT OR OTHERWISE,
  ARISING FROM, OUT OF OR IN CONNECTION WITH THE SOFTWARE OR THE USE OR
  OTHER DEALINGS IN THE SOFTWARE.

  For more information, please refer to <http://unlicense.org/>
*/
/**************************************************************************
 *
 * Copyright 2013-2014 RAD Game Tools and Valve Software
 * Copyright 2010-2014 Rich Geldreich and Tenacious Software LLC
 * All Rights Reserved.
 *
 * Permission is hereby granted, free of charge, to any person obtaining a copy
 * of this software and associated documentation files (the "Software"), to deal
 * in the Software without restriction, including without limitation the rights
 * to use, copy, modify, merge, publish, distribute, sublicense, and/or sell
 * copies of the Software, and to permit persons to whom the Software is
 * furnished to do so, subject to the following conditions:
 *
 * The above copyright notice and this permission notice shall be included in
 * all copies or substantial portions of the Software.
 *
 * THE SOFTWARE IS PROVIDED "AS IS", WITHOUT WARRANTY OF ANY KIND, EXPRESS OR
 * IMPLIED, INCLUDING BUT NOT LIMITED TO THE WARRANTIES OF MERCHANTABILITY,
 * FITNESS FOR A PARTICULAR PURPOSE AND NONINFRINGEMENT. IN NO EVENT SHALL THE
 * AUTHORS OR COPYRIGHT HOLDERS BE LIABLE FOR ANY CLAIM, DAMAGES OR OTHER
 * LIABILITY, WHETHER IN AN ACTION OF CONTRACT, TORT OR OTHERWISE, ARISING FROM,
 * OUT OF OR IN CONNECTION WITH THE SOFTWARE OR THE USE OR OTHER DEALINGS IN
 * THE SOFTWARE.
 *
 **************************************************************************/




#ifdef __cplusplus
extern "C" {
#endif

/* ------------------- Low-level Compression (independent from all decompression API's) */

/* Purposely making these tables static for faster init and thread safety. */
static const mz_uint16 s_tdefl_len_sym[256] =
    {
      257, 258, 259, 260, 261, 262, 263, 264, 265, 265, 266, 266, 267, 267, 268, 268, 269, 269, 269, 269, 270, 270, 270, 270, 271, 271, 271, 271, 272, 272, 272, 272,
      273, 273, 273, 273, 273, 273, 273, 273, 274, 274, 274, 274, 274, 274, 274, 274, 275, 275, 275, 275, 275, 275, 275, 275, 276, 276, 276, 276, 276, 276, 276, 276,
      277, 277, 277, 277, 277, 277, 277, 277, 277, 277, 277, 277, 277, 277, 277, 277, 278, 278, 278, 278, 278, 278, 278, 278, 278, 278, 278, 278, 278, 278, 278, 278,
      279, 279, 279, 279, 279, 279, 279, 279, 279, 279, 279, 279, 279, 279, 279, 279, 280, 280, 280, 280, 280, 280, 280, 280, 280, 280, 280, 280, 280, 280, 280, 280,
      281, 281, 281, 281, 281, 281, 281, 281, 281, 281, 281, 281, 281, 281, 281, 281, 281, 281, 281, 281, 281, 281, 281, 281, 281, 281, 281, 281, 281, 281, 281, 281,
      282, 282, 282, 282, 282, 282, 282, 282, 282, 282, 282, 282, 282, 282, 282, 282, 282, 282, 282, 282, 282, 282, 282, 282, 282, 282, 282, 282, 282, 282, 282, 282,
      283, 283, 283, 283, 283, 283, 283, 283, 283, 283, 283, 283, 283, 283, 283, 283, 283, 283, 283, 283, 283, 283, 283, 283, 283, 283, 283, 283, 283, 283, 283, 283,
      284, 284, 284, 284, 284, 284, 284, 284, 284, 284, 284, 284, 284, 284, 284, 284, 284, 284, 284, 284, 284, 284, 284, 284, 284, 284, 284, 284, 284, 284, 284, 285
    };

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
      13, 13, 13, 13, 13, 13, 13, 13, 13, 13, 13, 13, 13, 13, 13, 13, 13, 13, 13, 13, 13, 13, 13, 13, 13, 13, 13, 13, 13, 13, 13, 13
    };

/* Radix sorts tdefl_sym_freq[] array by 16-bit key m_key. Returns ptr to sorted values. */
typedef struct
{
    mz_uint16 m_key, m_sym_index;
} tdefl_sym_freq;
static tdefl_sym_freq *tdefl_radix_sort_syms(mz_uint num_syms, tdefl_sym_freq *pSyms0, tdefl_sym_freq *pSyms1)
{
    mz_uint32 total_passes = 2, pass_shift, pass, i, hist[256 * 2];
    tdefl_sym_freq *pCur_syms = pSyms0, *pNew_syms = pSyms1;
    MZ_CLEAR_OBJ(hist);
    for (i = 0; i < num_syms; i++)
    {
        mz_uint freq = pSyms0[i].m_key;
        hist[freq & 0xFF]++;
        hist[256 + ((freq >> 8) & 0xFF)]++;
    }
    while ((total_passes > 1) && (num_syms == hist[(total_passes - 1) * 256]))
        total_passes--;
    for (pass_shift = 0, pass = 0; pass < total_passes; pass++, pass_shift += 8)
    {
        const mz_uint32 *pHist = &hist[pass << 8];
        mz_uint offsets[256], cur_ofs = 0;
        for (i = 0; i < 256; i++)
        {
            offsets[i] = cur_ofs;
            cur_ofs += pHist[i];
        }
        for (i = 0; i < num_syms; i++)
            pNew_syms[offsets[(pCur_syms[i].m_key >> pass_shift) & 0xFF]++] = pCur_syms[i];
        {
            tdefl_sym_freq *t = pCur_syms;
            pCur_syms = pNew_syms;
            pNew_syms = t;
        }
    }
    return pCur_syms;
}

/* tdefl_calculate_minimum_redundancy() originally written by: Alistair Moffat, alistair@cs.mu.oz.au, Jyrki Katajainen, jyrki@diku.dk, November 1996. */
static void tdefl_calculate_minimum_redundancy(tdefl_sym_freq *A, int n)
{
    int root, leaf, next, avbl, used, dpth;
    if (n == 0)
        return;
    else if (n == 1)
    {
        A[0].m_key = 1;
        return;
    }
    A[0].m_key += A[1].m_key;
    root = 0;
    leaf = 2;
    for (next = 1; next < n - 1; next++)
    {
        if (leaf >= n || A[root].m_key < A[leaf].m_key)
        {
            A[next].m_key = A[root].m_key;
            A[root++].m_key = (mz_uint16)next;
        }
        else
            A[next].m_key = A[leaf++].m_key;
        if (leaf >= n || (root < next && A[root].m_key < A[leaf].m_key))
        {
            A[next].m_key = (mz_uint16)(A[next].m_key + A[root].m_key);
            A[root++].m_key = (mz_uint16)next;
        }
        else
            A[next].m_key = (mz_uint16)(A[next].m_key + A[leaf++].m_key);
    }
    A[n - 2].m_key = 0;
    for (next = n - 3; next >= 0; next--)
        A[next].m_key = A[A[next].m_key].m_key + 1;
    avbl = 1;
    used = dpth = 0;
    root = n - 2;
    next = n - 1;
    while (avbl > 0)
    {
        while (root >= 0 && (int)A[root].m_key == dpth)
        {
            used++;
            root--;
        }
        while (avbl > used)
        {
            A[next--].m_key = (mz_uint16)(dpth);
            avbl--;
        }
        avbl = 2 * used;
        dpth++;
        used = 0;
    }
}

/* Limits canonical Huffman code table's max code size. */
enum
{
    TDEFL_MAX_SUPPORTED_HUFF_CODESIZE = 32
};
static void tdefl_huffman_enforce_max_code_size(int *pNum_codes, int code_list_len, int max_code_size)
{
    int i;
    mz_uint32 total = 0;
    if (code_list_len <= 1)
        return;
    for (i = max_code_size + 1; i <= TDEFL_MAX_SUPPORTED_HUFF_CODESIZE; i++)
        pNum_codes[max_code_size] += pNum_codes[i];
    for (i = max_code_size; i > 0; i--)
        total += (((mz_uint32)pNum_codes[i]) << (max_code_size - i));
    while (total != (1UL << max_code_size))
    {
        pNum_codes[max_code_size]--;
        for (i = max_code_size - 1; i > 0; i--)
            if (pNum_codes[i])
            {
                pNum_codes[i]--;
                pNum_codes[i + 1] += 2;
                break;
            }
        total--;
    }
}

static void tdefl_optimize_huffman_table(tdefl_compressor *d, int table_num, int table_len, int code_size_limit, int static_table)
{
    int i, j, l, num_codes[1 + TDEFL_MAX_SUPPORTED_HUFF_CODESIZE];
    mz_uint next_code[TDEFL_MAX_SUPPORTED_HUFF_CODESIZE + 1];
    MZ_CLEAR_OBJ(num_codes);
    if (static_table)
    {
        for (i = 0; i < table_len; i++)
            num_codes[d->m_huff_code_sizes[table_num][i]]++;
    }
    else
    {
        tdefl_sym_freq syms0[TDEFL_MAX_HUFF_SYMBOLS], syms1[TDEFL_MAX_HUFF_SYMBOLS], *pSyms;
        int num_used_syms = 0;
        const mz_uint16 *pSym_count = &d->m_huff_count[table_num][0];
        for (i = 0; i < table_len; i++)
            if (pSym_count[i])
            {
                syms0[num_used_syms].m_key = (mz_uint16)pSym_count[i];
                syms0[num_used_syms++].m_sym_index = (mz_uint16)i;
            }

        pSyms = tdefl_radix_sort_syms(num_used_syms, syms0, syms1);
        tdefl_calculate_minimum_redundancy(pSyms, num_used_syms);

        for (i = 0; i < num_used_syms; i++)
            num_codes[pSyms[i].m_key]++;

        tdefl_huffman_enforce_max_code_size(num_codes, num_used_syms, code_size_limit);

        MZ_CLEAR_OBJ(d->m_huff_code_sizes[table_num]);
        MZ_CLEAR_OBJ(d->m_huff_codes[table_num]);
        for (i = 1, j = num_used_syms; i <= code_size_limit; i++)
            for (l = num_codes[i]; l > 0; l--)
                d->m_huff_code_sizes[table_num][pSyms[--j].m_sym_index] = (mz_uint8)(i);
    }

    next_code[1] = 0;
    for (j = 0, i = 2; i <= code_size_limit; i++)
        next_code[i] = j = ((j + num_codes[i - 1]) << 1);

    for (i = 0; i < table_len; i++)
    {
        mz_uint rev_code = 0, code, code_size;
        if ((code_size = d->m_huff_code_sizes[table_num][i]) == 0)
            continue;
        code = next_code[code_size]++;
        for (l = code_size; l > 0; l--, code >>= 1)
            rev_code = (rev_code << 1) | (code & 1);
        d->m_huff_codes[table_num][i] = (mz_uint16)rev_code;
    }
}

#define TDEFL_PUT_BITS(b, l)                                       \
    do                                                             \
    {                                                              \
        mz_uint bits = b;                                          \
        mz_uint len = l;                                           \
        MZ_ASSERT(bits <= ((1U << len) - 1U));                     \
        d->m_bit_buffer |= (bits << d->m_bits_in);                 \
        d->m_bits_in += len;                                       \
        while (d->m_bits_in >= 8)                                  \
        {                                                          \
            if (d->m_pOutput_buf < d->m_pOutput_buf_end)           \
                *d->m_pOutput_buf++ = (mz_uint8)(d->m_bit_buffer); \
            d->m_bit_buffer >>= 8;                                 \
            d->m_bits_in -= 8;                                     \
        }                                                          \
    }                                                              \
    MZ_MACRO_END

#define TDEFL_RLE_PREV_CODE_SIZE()                                                                                       \
    {                                                                                                                    \
        if (rle_repeat_count)                                                                                            \
        {                                                                                                                \
            if (rle_repeat_count < 3)                                                                                    \
            {                                                                                                            \
                d->m_huff_count[2][prev_code_size] = (mz_uint16)(d->m_huff_count[2][prev_code_size] + rle_repeat_count); \
                while (rle_repeat_count--)                                                                               \
                    packed_code_sizes[num_packed_code_sizes++] = prev_code_size;                                         \
            }                                                                                                            \
            else                                                                                                         \
            {                                                                                                            \
                d->m_huff_count[2][16] = (mz_uint16)(d->m_huff_count[2][16] + 1);                                        \
                packed_code_sizes[num_packed_code_sizes++] = 16;                                                         \
                packed_code_sizes[num_packed_code_sizes++] = (mz_uint8)(rle_repeat_count - 3);                           \
            }                                                                                                            \
            rle_repeat_count = 0;                                                                                        \
        }                                                                                                                \
    }

#define TDEFL_RLE_ZERO_CODE_SIZE()                                                         \
    {                                                                                      \
        if (rle_z_count)                                                                   \
        {                                                                                  \
            if (rle_z_count < 3)                                                           \
            {                                                                              \
                d->m_huff_count[2][0] = (mz_uint16)(d->m_huff_count[2][0] + rle_z_count);  \
                while (rle_z_count--)                                                      \
                    packed_code_sizes[num_packed_code_sizes++] = 0;                        \
            }                                                                              \
            else if (rle_z_count <= 10)                                                    \
            {                                                                              \
                d->m_huff_count[2][17] = (mz_uint16)(d->m_huff_count[2][17] + 1);          \
                packed_code_sizes[num_packed_code_sizes++] = 17;                           \
                packed_code_sizes[num_packed_code_sizes++] = (mz_uint8)(rle_z_count - 3);  \
            }                                                                              \
            else                                                                           \
            {                                                                              \
                d->m_huff_count[2][18] = (mz_uint16)(d->m_huff_count[2][18] + 1);          \
                packed_code_sizes[num_packed_code_sizes++] = 18;                           \
                packed_code_sizes[num_packed_code_sizes++] = (mz_uint8)(rle_z_count - 11); \
            }                                                                              \
            rle_z_count = 0;                                                               \
        }                                                                                  \
    }

static mz_uint8 s_tdefl_packed_code_size_syms_swizzle[] = { 16, 17, 18, 0, 8, 7, 9, 6, 10, 5, 11, 4, 12, 3, 13, 2, 14, 1, 15 };

static void tdefl_start_dynamic_block(tdefl_compressor *d)
{
    int num_lit_codes, num_dist_codes, num_bit_lengths;
    mz_uint i, total_code_sizes_to_pack, num_packed_code_sizes, rle_z_count, rle_repeat_count, packed_code_sizes_index;
    mz_uint8 code_sizes_to_pack[TDEFL_MAX_HUFF_SYMBOLS_0 + TDEFL_MAX_HUFF_SYMBOLS_1], packed_code_sizes[TDEFL_MAX_HUFF_SYMBOLS_0 + TDEFL_MAX_HUFF_SYMBOLS_1], prev_code_size = 0xFF;

    d->m_huff_count[0][256] = 1;

    tdefl_optimize_huffman_table(d, 0, TDEFL_MAX_HUFF_SYMBOLS_0, 15, MZ_FALSE);
    tdefl_optimize_huffman_table(d, 1, TDEFL_MAX_HUFF_SYMBOLS_1, 15, MZ_FALSE);

    for (num_lit_codes = 286; num_lit_codes > 257; num_lit_codes--)
        if (d->m_huff_code_sizes[0][num_lit_codes - 1])
            break;
    for (num_dist_codes = 30; num_dist_codes > 1; num_dist_codes--)
        if (d->m_huff_code_sizes[1][num_dist_codes - 1])
            break;

    memcpy(code_sizes_to_pack, &d->m_huff_code_sizes[0][0], num_lit_codes);
    memcpy(code_sizes_to_pack + num_lit_codes, &d->m_huff_code_sizes[1][0], num_dist_codes);
    total_code_sizes_to_pack = num_lit_codes + num_dist_codes;
    num_packed_code_sizes = 0;
    rle_z_count = 0;
    rle_repeat_count = 0;

    memset(&d->m_huff_count[2][0], 0, sizeof(d->m_huff_count[2][0]) * TDEFL_MAX_HUFF_SYMBOLS_2);
    for (i = 0; i < total_code_sizes_to_pack; i++)
    {
        mz_uint8 code_size = code_sizes_to_pack[i];
        if (!code_size)
        {
            TDEFL_RLE_PREV_CODE_SIZE();
            if (++rle_z_count == 138)
            {
                TDEFL_RLE_ZERO_CODE_SIZE();
            }
        }
        else
        {
            TDEFL_RLE_ZERO_CODE_SIZE();
            if (code_size != prev_code_size)
            {
                TDEFL_RLE_PREV_CODE_SIZE();
                d->m_huff_count[2][code_size] = (mz_uint16)(d->m_huff_count[2][code_size] + 1);
                packed_code_sizes[num_packed_code_sizes++] = code_size;
            }
            else if (++rle_repeat_count == 6)
            {
                TDEFL_RLE_PREV_CODE_SIZE();
            }
        }
        prev_code_size = code_size;
    }
    if (rle_repeat_count)
    {
        TDEFL_RLE_PREV_CODE_SIZE();
    }
    else
    {
        TDEFL_RLE_ZERO_CODE_SIZE();
    }

    tdefl_optimize_huffman_table(d, 2, TDEFL_MAX_HUFF_SYMBOLS_2, 7, MZ_FALSE);

    TDEFL_PUT_BITS(2, 2);

    TDEFL_PUT_BITS(num_lit_codes - 257, 5);
    TDEFL_PUT_BITS(num_dist_codes - 1, 5);

    for (num_bit_lengths = 18; num_bit_lengths >= 0; num_bit_lengths--)
        if (d->m_huff_code_sizes[2][s_tdefl_packed_code_size_syms_swizzle[num_bit_lengths]])
            break;
    num_bit_lengths = MZ_MAX(4, (num_bit_lengths + 1));
    TDEFL_PUT_BITS(num_bit_lengths - 4, 4);
    for (i = 0; (int)i < num_bit_lengths; i++)
        TDEFL_PUT_BITS(d->m_huff_code_sizes[2][s_tdefl_packed_code_size_syms_swizzle[i]], 3);

    for (packed_code_sizes_index = 0; packed_code_sizes_index < num_packed_code_sizes;)
    {
        mz_uint code = packed_code_sizes[packed_code_sizes_index++];
        MZ_ASSERT(code < TDEFL_MAX_HUFF_SYMBOLS_2);
        TDEFL_PUT_BITS(d->m_huff_codes[2][code], d->m_huff_code_sizes[2][code]);
        if (code >= 16)
            TDEFL_PUT_BITS(packed_code_sizes[packed_code_sizes_index++], "\02\03\07"[code - 16]);
    }
}

static void tdefl_start_static_block(tdefl_compressor *d)
{
    mz_uint i;
    mz_uint8 *p = &d->m_huff_code_sizes[0][0];

    for (i = 0; i <= 143; ++i)
        *p++ = 8;
    for (; i <= 255; ++i)
        *p++ = 9;
    for (; i <= 279; ++i)
        *p++ = 7;
    for (; i <= 287; ++i)
        *p++ = 8;

    memset(d->m_huff_code_sizes[1], 5, 32);

    tdefl_optimize_huffman_table(d, 0, 288, 15, MZ_TRUE);
    tdefl_optimize_huffman_table(d, 1, 32, 15, MZ_TRUE);

    TDEFL_PUT_BITS(1, 2);
}

static const mz_uint mz_bitmasks[17] = { 0x0000, 0x0001, 0x0003, 0x0007, 0x000F, 0x001F, 0x003F, 0x007F, 0x00FF, 0x01FF, 0x03FF, 0x07FF, 0x0FFF, 0x1FFF, 0x3FFF, 0x7FFF, 0xFFFF };

#if MINIZ_USE_UNALIGNED_LOADS_AND_STORES && MINIZ_LITTLE_ENDIAN && MINIZ_HAS_64BIT_REGISTERS
static mz_bool tdefl_compress_lz_codes(tdefl_compressor *d)
{
    mz_uint flags;
    mz_uint8 *pLZ_codes;
    mz_uint8 *pOutput_buf = d->m_pOutput_buf;
    mz_uint8 *pLZ_code_buf_end = d->m_pLZ_code_buf;
    mz_uint64 bit_buffer = d->m_bit_buffer;
    mz_uint bits_in = d->m_bits_in;

#define TDEFL_PUT_BITS_FAST(b, l)                    \
    {                                                \
        bit_buffer |= (((mz_uint64)(b)) << bits_in); \
        bits_in += (l);                              \
    }

    flags = 1;
    for (pLZ_codes = d->m_lz_code_buf; pLZ_codes < pLZ_code_buf_end; flags >>= 1)
    {
        if (flags == 1)
            flags = *pLZ_codes++ | 0x100;

        if (flags & 1)
        {
            mz_uint s0, s1, n0, n1, sym, num_extra_bits;
            mz_uint match_len = pLZ_codes[0], match_dist = *(const mz_uint16 *)(pLZ_codes + 1);
            pLZ_codes += 3;

            MZ_ASSERT(d->m_huff_code_sizes[0][s_tdefl_len_sym[match_len]]);
            TDEFL_PUT_BITS_FAST(d->m_huff_codes[0][s_tdefl_len_sym[match_len]], d->m_huff_code_sizes[0][s_tdefl_len_sym[match_len]]);
            TDEFL_PUT_BITS_FAST(match_len & mz_bitmasks[s_tdefl_len_extra[match_len]], s_tdefl_len_extra[match_len]);

            /* This sequence coaxes MSVC into using cmov's vs. jmp's. */
            s0 = s_tdefl_small_dist_sym[match_dist & 511];
            n0 = s_tdefl_small_dist_extra[match_dist & 511];
            s1 = s_tdefl_large_dist_sym[match_dist >> 8];
            n1 = s_tdefl_large_dist_extra[match_dist >> 8];
            sym = (match_dist < 512) ? s0 : s1;
            num_extra_bits = (match_dist < 512) ? n0 : n1;

            MZ_ASSERT(d->m_huff_code_sizes[1][sym]);
            TDEFL_PUT_BITS_FAST(d->m_huff_codes[1][sym], d->m_huff_code_sizes[1][sym]);
            TDEFL_PUT_BITS_FAST(match_dist & mz_bitmasks[num_extra_bits], num_extra_bits);
        }
        else
        {
            mz_uint lit = *pLZ_codes++;
            MZ_ASSERT(d->m_huff_code_sizes[0][lit]);
            TDEFL_PUT_BITS_FAST(d->m_huff_codes[0][lit], d->m_huff_code_sizes[0][lit]);

            if (((flags & 2) == 0) && (pLZ_codes < pLZ_code_buf_end))
            {
                flags >>= 1;
                lit = *pLZ_codes++;
                MZ_ASSERT(d->m_huff_code_sizes[0][lit]);
                TDEFL_PUT_BITS_FAST(d->m_huff_codes[0][lit], d->m_huff_code_sizes[0][lit]);

                if (((flags & 2) == 0) && (pLZ_codes < pLZ_code_buf_end))
                {
                    flags >>= 1;
                    lit = *pLZ_codes++;
                    MZ_ASSERT(d->m_huff_code_sizes[0][lit]);
                    TDEFL_PUT_BITS_FAST(d->m_huff_codes[0][lit], d->m_huff_code_sizes[0][lit]);
                }
            }
        }

        if (pOutput_buf >= d->m_pOutput_buf_end)
            return MZ_FALSE;

        *(mz_uint64 *)pOutput_buf = bit_buffer;
        pOutput_buf += (bits_in >> 3);
        bit_buffer >>= (bits_in & ~7);
        bits_in &= 7;
    }

#undef TDEFL_PUT_BITS_FAST

    d->m_pOutput_buf = pOutput_buf;
    d->m_bits_in = 0;
    d->m_bit_buffer = 0;

    while (bits_in)
    {
        mz_uint32 n = MZ_MIN(bits_in, 16);
        TDEFL_PUT_BITS((mz_uint)bit_buffer & mz_bitmasks[n], n);
        bit_buffer >>= n;
        bits_in -= n;
    }

    TDEFL_PUT_BITS(d->m_huff_codes[0][256], d->m_huff_code_sizes[0][256]);

    return (d->m_pOutput_buf < d->m_pOutput_buf_end);
}
#else
static mz_bool tdefl_compress_lz_codes(tdefl_compressor *d)
{
    mz_uint flags;
    mz_uint8 *pLZ_codes;

    flags = 1;
    for (pLZ_codes = d->m_lz_code_buf; pLZ_codes < d->m_pLZ_code_buf; flags >>= 1)
    {
        if (flags == 1)
            flags = *pLZ_codes++ | 0x100;
        if (flags & 1)
        {
            mz_uint sym, num_extra_bits;
            mz_uint match_len = pLZ_codes[0], match_dist = (pLZ_codes[1] | (pLZ_codes[2] << 8));
            pLZ_codes += 3;

            MZ_ASSERT(d->m_huff_code_sizes[0][s_tdefl_len_sym[match_len]]);
            TDEFL_PUT_BITS(d->m_huff_codes[0][s_tdefl_len_sym[match_len]], d->m_huff_code_sizes[0][s_tdefl_len_sym[match_len]]);
            TDEFL_PUT_BITS(match_len & mz_bitmasks[s_tdefl_len_extra[match_len]], s_tdefl_len_extra[match_len]);

            if (match_dist < 512)
            {
                sym = s_tdefl_small_dist_sym[match_dist];
                num_extra_bits = s_tdefl_small_dist_extra[match_dist];
            }
            else
            {
                sym = s_tdefl_large_dist_sym[match_dist >> 8];
                num_extra_bits = s_tdefl_large_dist_extra[match_dist >> 8];
            }
            MZ_ASSERT(d->m_huff_code_sizes[1][sym]);
            TDEFL_PUT_BITS(d->m_huff_codes[1][sym], d->m_huff_code_sizes[1][sym]);
            TDEFL_PUT_BITS(match_dist & mz_bitmasks[num_extra_bits], num_extra_bits);
        }
        else
        {
            mz_uint lit = *pLZ_codes++;
            MZ_ASSERT(d->m_huff_code_sizes[0][lit]);
            TDEFL_PUT_BITS(d->m_huff_codes[0][lit], d->m_huff_code_sizes[0][lit]);
        }
    }

    TDEFL_PUT_BITS(d->m_huff_codes[0][256], d->m_huff_code_sizes[0][256]);

    return (d->m_pOutput_buf < d->m_pOutput_buf_end);
}
#endif /* MINIZ_USE_UNALIGNED_LOADS_AND_STORES && MINIZ_LITTLE_ENDIAN && MINIZ_HAS_64BIT_REGISTERS */

static mz_bool tdefl_compress_block(tdefl_compressor *d, mz_bool static_block)
{
    if (static_block)
        tdefl_start_static_block(d);
    else
        tdefl_start_dynamic_block(d);
    return tdefl_compress_lz_codes(d);
}

static int tdefl_flush_block(tdefl_compressor *d, int flush)
{
    mz_uint saved_bit_buf, saved_bits_in;
    mz_uint8 *pSaved_output_buf;
    mz_bool comp_block_succeeded = MZ_FALSE;
    int n, use_raw_block = ((d->m_flags & TDEFL_FORCE_ALL_RAW_BLOCKS) != 0) && (d->m_lookahead_pos - d->m_lz_code_buf_dict_pos) <= d->m_dict_size;
    mz_uint8 *pOutput_buf_start = ((d->m_pPut_buf_func == NULL) && ((*d->m_pOut_buf_size - d->m_out_buf_ofs) >= TDEFL_OUT_BUF_SIZE)) ? ((mz_uint8 *)d->m_pOut_buf + d->m_out_buf_ofs) : d->m_output_buf;

    d->m_pOutput_buf = pOutput_buf_start;
    d->m_pOutput_buf_end = d->m_pOutput_buf + TDEFL_OUT_BUF_SIZE - 16;

    MZ_ASSERT(!d->m_output_flush_remaining);
    d->m_output_flush_ofs = 0;
    d->m_output_flush_remaining = 0;

    *d->m_pLZ_flags = (mz_uint8)(*d->m_pLZ_flags >> d->m_num_flags_left);
    d->m_pLZ_code_buf -= (d->m_num_flags_left == 8);

    if ((d->m_flags & TDEFL_WRITE_ZLIB_HEADER) && (!d->m_block_index))
    {
        TDEFL_PUT_BITS(0x78, 8);
        TDEFL_PUT_BITS(0x01, 8);
    }

    TDEFL_PUT_BITS(flush == TDEFL_FINISH, 1);

    pSaved_output_buf = d->m_pOutput_buf;
    saved_bit_buf = d->m_bit_buffer;
    saved_bits_in = d->m_bits_in;

    if (!use_raw_block)
        comp_block_succeeded = tdefl_compress_block(d, (d->m_flags & TDEFL_FORCE_ALL_STATIC_BLOCKS) || (d->m_total_lz_bytes < 48));

    /* If the block gets expanded, forget the current contents of the output buffer and send a raw block instead. */
    if (((use_raw_block) || ((d->m_total_lz_bytes) && ((d->m_pOutput_buf - pSaved_output_buf + 1U) >= d->m_total_lz_bytes))) &&
        ((d->m_lookahead_pos - d->m_lz_code_buf_dict_pos) <= d->m_dict_size))
    {
        mz_uint i;
        d->m_pOutput_buf = pSaved_output_buf;
        d->m_bit_buffer = saved_bit_buf, d->m_bits_in = saved_bits_in;
        TDEFL_PUT_BITS(0, 2);
        if (d->m_bits_in)
        {
            TDEFL_PUT_BITS(0, 8 - d->m_bits_in);
        }
        for (i = 2; i; --i, d->m_total_lz_bytes ^= 0xFFFF)
        {
            TDEFL_PUT_BITS(d->m_total_lz_bytes & 0xFFFF, 16);
        }
        for (i = 0; i < d->m_total_lz_bytes; ++i)
        {
            TDEFL_PUT_BITS(d->m_dict[(d->m_lz_code_buf_dict_pos + i) & TDEFL_LZ_DICT_SIZE_MASK], 8);
        }
    }
    /* Check for the extremely unlikely (if not impossible) case of the compressed block not fitting into the output buffer when using dynamic codes. */
    else if (!comp_block_succeeded)
    {
        d->m_pOutput_buf = pSaved_output_buf;
        d->m_bit_buffer = saved_bit_buf, d->m_bits_in = saved_bits_in;
        tdefl_compress_block(d, MZ_TRUE);
    }

    if (flush)
    {
        if (flush == TDEFL_FINISH)
        {
            if (d->m_bits_in)
            {
                TDEFL_PUT_BITS(0, 8 - d->m_bits_in);
            }
            if (d->m_flags & TDEFL_WRITE_ZLIB_HEADER)
            {
                mz_uint i, a = d->m_adler32;
                for (i = 0; i < 4; i++)
                {
                    TDEFL_PUT_BITS((a >> 24) & 0xFF, 8);
                    a <<= 8;
                }
            }
        }
        else
        {
            mz_uint i, z = 0;
            TDEFL_PUT_BITS(0, 3);
            if (d->m_bits_in)
            {
                TDEFL_PUT_BITS(0, 8 - d->m_bits_in);
            }
            for (i = 2; i; --i, z ^= 0xFFFF)
            {
                TDEFL_PUT_BITS(z & 0xFFFF, 16);
            }
        }
    }

    MZ_ASSERT(d->m_pOutput_buf < d->m_pOutput_buf_end);

    memset(&d->m_huff_count[0][0], 0, sizeof(d->m_huff_count[0][0]) * TDEFL_MAX_HUFF_SYMBOLS_0);
    memset(&d->m_huff_count[1][0], 0, sizeof(d->m_huff_count[1][0]) * TDEFL_MAX_HUFF_SYMBOLS_1);

    d->m_pLZ_code_buf = d->m_lz_code_buf + 1;
    d->m_pLZ_flags = d->m_lz_code_buf;
    d->m_num_flags_left = 8;
    d->m_lz_code_buf_dict_pos += d->m_total_lz_bytes;
    d->m_total_lz_bytes = 0;
    d->m_block_index++;

    if ((n = (int)(d->m_pOutput_buf - pOutput_buf_start)) != 0)
    {
        if (d->m_pPut_buf_func)
        {
            *d->m_pIn_buf_size = d->m_pSrc - (const mz_uint8 *)d->m_pIn_buf;
            if (!(*d->m_pPut_buf_func)(d->m_output_buf, n, d->m_pPut_buf_user))
                return (d->m_prev_return_status = TDEFL_STATUS_PUT_BUF_FAILED);
        }
        else if (pOutput_buf_start == d->m_output_buf)
        {
            int bytes_to_copy = (int)MZ_MIN((size_t)n, (size_t)(*d->m_pOut_buf_size - d->m_out_buf_ofs));
            memcpy((mz_uint8 *)d->m_pOut_buf + d->m_out_buf_ofs, d->m_output_buf, bytes_to_copy);
            d->m_out_buf_ofs += bytes_to_copy;
            if ((n -= bytes_to_copy) != 0)
            {
                d->m_output_flush_ofs = bytes_to_copy;
                d->m_output_flush_remaining = n;
            }
        }
        else
        {
            d->m_out_buf_ofs += n;
        }
    }

    return d->m_output_flush_remaining;
}

#if MINIZ_USE_UNALIGNED_LOADS_AND_STORES
#ifdef MINIZ_UNALIGNED_USE_MEMCPY
static mz_uint16 TDEFL_READ_UNALIGNED_WORD(const mz_uint8* p)
{
	mz_uint16 ret;
	memcpy(&ret, p, sizeof(mz_uint16));
	return ret;
}
static mz_uint16 TDEFL_READ_UNALIGNED_WORD2(const mz_uint16* p)
{
	mz_uint16 ret;
	memcpy(&ret, p, sizeof(mz_uint16));
	return ret;
}
#else
#define TDEFL_READ_UNALIGNED_WORD(p) *(const mz_uint16 *)(p)
#define TDEFL_READ_UNALIGNED_WORD2(p) *(const mz_uint16 *)(p)
#endif
static MZ_FORCEINLINE void tdefl_find_match(tdefl_compressor *d, mz_uint lookahead_pos, mz_uint max_dist, mz_uint max_match_len, mz_uint *pMatch_dist, mz_uint *pMatch_len)
{
    mz_uint dist, pos = lookahead_pos & TDEFL_LZ_DICT_SIZE_MASK, match_len = *pMatch_len, probe_pos = pos, next_probe_pos, probe_len;
    mz_uint num_probes_left = d->m_max_probes[match_len >= 32];
    const mz_uint16 *s = (const mz_uint16 *)(d->m_dict + pos), *p, *q;
    mz_uint16 c01 = TDEFL_READ_UNALIGNED_WORD(&d->m_dict[pos + match_len - 1]), s01 = TDEFL_READ_UNALIGNED_WORD2(s);
    MZ_ASSERT(max_match_len <= TDEFL_MAX_MATCH_LEN);
    if (max_match_len <= match_len)
        return;
    for (;;)
    {
        for (;;)
        {
            if (--num_probes_left == 0)
                return;
#define TDEFL_PROBE                                                                             \
    next_probe_pos = d->m_next[probe_pos];                                                      \
    if ((!next_probe_pos) || ((dist = (mz_uint16)(lookahead_pos - next_probe_pos)) > max_dist)) \
        return;                                                                                 \
    probe_pos = next_probe_pos & TDEFL_LZ_DICT_SIZE_MASK;                                       \
    if (TDEFL_READ_UNALIGNED_WORD(&d->m_dict[probe_pos + match_len - 1]) == c01)                \
        break;
            TDEFL_PROBE;
            TDEFL_PROBE;
            TDEFL_PROBE;
        }
        if (!dist)
            break;
        q = (const mz_uint16 *)(d->m_dict + probe_pos);
        if (TDEFL_READ_UNALIGNED_WORD2(q) != s01)
            continue;
        p = s;
        probe_len = 32;
        do
        {
        } while ((TDEFL_READ_UNALIGNED_WORD2(++p) == TDEFL_READ_UNALIGNED_WORD2(++q)) && (TDEFL_READ_UNALIGNED_WORD2(++p) == TDEFL_READ_UNALIGNED_WORD2(++q)) &&
                 (TDEFL_READ_UNALIGNED_WORD2(++p) == TDEFL_READ_UNALIGNED_WORD2(++q)) && (TDEFL_READ_UNALIGNED_WORD2(++p) == TDEFL_READ_UNALIGNED_WORD2(++q)) && (--probe_len > 0));
        if (!probe_len)
        {
            *pMatch_dist = dist;
            *pMatch_len = MZ_MIN(max_match_len, (mz_uint)TDEFL_MAX_MATCH_LEN);
            break;
        }
        else if ((probe_len = ((mz_uint)(p - s) * 2) + (mz_uint)(*(const mz_uint8 *)p == *(const mz_uint8 *)q)) > match_len)
        {
            *pMatch_dist = dist;
            if ((*pMatch_len = match_len = MZ_MIN(max_match_len, probe_len)) == max_match_len)
                break;
            c01 = TDEFL_READ_UNALIGNED_WORD(&d->m_dict[pos + match_len - 1]);
        }
    }
}
#else
static MZ_FORCEINLINE void tdefl_find_match(tdefl_compressor *d, mz_uint lookahead_pos, mz_uint max_dist, mz_uint max_match_len, mz_uint *pMatch_dist, mz_uint *pMatch_len)
{
    mz_uint dist, pos = lookahead_pos & TDEFL_LZ_DICT_SIZE_MASK, match_len = *pMatch_len, probe_pos = pos, next_probe_pos, probe_len;
    mz_uint num_probes_left = d->m_max_probes[match_len >= 32];
    const mz_uint8 *s = d->m_dict + pos, *p, *q;
    mz_uint8 c0 = d->m_dict[pos + match_len], c1 = d->m_dict[pos + match_len - 1];
    MZ_ASSERT(max_match_len <= TDEFL_MAX_MATCH_LEN);
    if (max_match_len <= match_len)
        return;
    for (;;)
    {
        for (;;)
        {
            if (--num_probes_left == 0)
                return;
#define TDEFL_PROBE                                                                               \
    next_probe_pos = d->m_next[probe_pos];                                                        \
    if ((!next_probe_pos) || ((dist = (mz_uint16)(lookahead_pos - next_probe_pos)) > max_dist))   \
        return;                                                                                   \
    probe_pos = next_probe_pos & TDEFL_LZ_DICT_SIZE_MASK;                                         \
    if ((d->m_dict[probe_pos + match_len] == c0) && (d->m_dict[probe_pos + match_len - 1] == c1)) \
        break;
            TDEFL_PROBE;
            TDEFL_PROBE;
            TDEFL_PROBE;
        }
        if (!dist)
            break;
        p = s;
        q = d->m_dict + probe_pos;
        for (probe_len = 0; probe_len < max_match_len; probe_len++)
            if (*p++ != *q++)
                break;
        if (probe_len > match_len)
        {
            *pMatch_dist = dist;
            if ((*pMatch_len = match_len = probe_len) == max_match_len)
                return;
            c0 = d->m_dict[pos + match_len];
            c1 = d->m_dict[pos + match_len - 1];
        }
    }
}
#endif /* #if MINIZ_USE_UNALIGNED_LOADS_AND_STORES */

#if MINIZ_USE_UNALIGNED_LOADS_AND_STORES && MINIZ_LITTLE_ENDIAN
#ifdef MINIZ_UNALIGNED_USE_MEMCPY
static mz_uint32 TDEFL_READ_UNALIGNED_WORD32(const mz_uint8* p)
{
	mz_uint32 ret;
	memcpy(&ret, p, sizeof(mz_uint32));
	return ret;
}
#else
#define TDEFL_READ_UNALIGNED_WORD32(p) *(const mz_uint32 *)(p)
#endif
static mz_bool tdefl_compress_fast(tdefl_compressor *d)
{
    /* Faster, minimally featured LZRW1-style match+parse loop with better register utilization. Intended for applications where raw throughput is valued more highly than ratio. */
    mz_uint lookahead_pos = d->m_lookahead_pos, lookahead_size = d->m_lookahead_size, dict_size = d->m_dict_size, total_lz_bytes = d->m_total_lz_bytes, num_flags_left = d->m_num_flags_left;
    mz_uint8 *pLZ_code_buf = d->m_pLZ_code_buf, *pLZ_flags = d->m_pLZ_flags;
    mz_uint cur_pos = lookahead_pos & TDEFL_LZ_DICT_SIZE_MASK;

    while ((d->m_src_buf_left) || ((d->m_flush) && (lookahead_size)))
    {
        const mz_uint TDEFL_COMP_FAST_LOOKAHEAD_SIZE = 4096;
        mz_uint dst_pos = (lookahead_pos + lookahead_size) & TDEFL_LZ_DICT_SIZE_MASK;
        mz_uint num_bytes_to_process = (mz_uint)MZ_MIN(d->m_src_buf_left, TDEFL_COMP_FAST_LOOKAHEAD_SIZE - lookahead_size);
        d->m_src_buf_left -= num_bytes_to_process;
        lookahead_size += num_bytes_to_process;

        while (num_bytes_to_process)
        {
            mz_uint32 n = MZ_MIN(TDEFL_LZ_DICT_SIZE - dst_pos, num_bytes_to_process);
            memcpy(d->m_dict + dst_pos, d->m_pSrc, n);
            if (dst_pos < (TDEFL_MAX_MATCH_LEN - 1))
                memcpy(d->m_dict + TDEFL_LZ_DICT_SIZE + dst_pos, d->m_pSrc, MZ_MIN(n, (TDEFL_MAX_MATCH_LEN - 1) - dst_pos));
            d->m_pSrc += n;
            dst_pos = (dst_pos + n) & TDEFL_LZ_DICT_SIZE_MASK;
            num_bytes_to_process -= n;
        }

        dict_size = MZ_MIN(TDEFL_LZ_DICT_SIZE - lookahead_size, dict_size);
        if ((!d->m_flush) && (lookahead_size < TDEFL_COMP_FAST_LOOKAHEAD_SIZE))
            break;

        while (lookahead_size >= 4)
        {
            mz_uint cur_match_dist, cur_match_len = 1;
            mz_uint8 *pCur_dict = d->m_dict + cur_pos;
            mz_uint first_trigram = TDEFL_READ_UNALIGNED_WORD32(pCur_dict) & 0xFFFFFF;
            mz_uint hash = (first_trigram ^ (first_trigram >> (24 - (TDEFL_LZ_HASH_BITS - 8)))) & TDEFL_LEVEL1_HASH_SIZE_MASK;
            mz_uint probe_pos = d->m_hash[hash];
            d->m_hash[hash] = (mz_uint16)lookahead_pos;

            if (((cur_match_dist = (mz_uint16)(lookahead_pos - probe_pos)) <= dict_size) && ((TDEFL_READ_UNALIGNED_WORD32(d->m_dict + (probe_pos &= TDEFL_LZ_DICT_SIZE_MASK)) & 0xFFFFFF) == first_trigram))
            {
                const mz_uint16 *p = (const mz_uint16 *)pCur_dict;
                const mz_uint16 *q = (const mz_uint16 *)(d->m_dict + probe_pos);
                mz_uint32 probe_len = 32;
                do
                {
                } while ((TDEFL_READ_UNALIGNED_WORD2(++p) == TDEFL_READ_UNALIGNED_WORD2(++q)) && (TDEFL_READ_UNALIGNED_WORD2(++p) == TDEFL_READ_UNALIGNED_WORD2(++q)) &&
                         (TDEFL_READ_UNALIGNED_WORD2(++p) == TDEFL_READ_UNALIGNED_WORD2(++q)) && (TDEFL_READ_UNALIGNED_WORD2(++p) == TDEFL_READ_UNALIGNED_WORD2(++q)) && (--probe_len > 0));
                cur_match_len = ((mz_uint)(p - (const mz_uint16 *)pCur_dict) * 2) + (mz_uint)(*(const mz_uint8 *)p == *(const mz_uint8 *)q);
                if (!probe_len)
                    cur_match_len = cur_match_dist ? TDEFL_MAX_MATCH_LEN : 0;

                if ((cur_match_len < TDEFL_MIN_MATCH_LEN) || ((cur_match_len == TDEFL_MIN_MATCH_LEN) && (cur_match_dist >= 8U * 1024U)))
                {
                    cur_match_len = 1;
                    *pLZ_code_buf++ = (mz_uint8)first_trigram;
                    *pLZ_flags = (mz_uint8)(*pLZ_flags >> 1);
                    d->m_huff_count[0][(mz_uint8)first_trigram]++;
                }
                else
                {
                    mz_uint32 s0, s1;
                    cur_match_len = MZ_MIN(cur_match_len, lookahead_size);

                    MZ_ASSERT((cur_match_len >= TDEFL_MIN_MATCH_LEN) && (cur_match_dist >= 1) && (cur_match_dist <= TDEFL_LZ_DICT_SIZE));

                    cur_match_dist--;

                    pLZ_code_buf[0] = (mz_uint8)(cur_match_len - TDEFL_MIN_MATCH_LEN);
#ifdef MINIZ_UNALIGNED_USE_MEMCPY
					memcpy(&pLZ_code_buf[1], &cur_match_dist, sizeof(cur_match_dist));
#else
                    *(mz_uint16 *)(&pLZ_code_buf[1]) = (mz_uint16)cur_match_dist;
#endif
                    pLZ_code_buf += 3;
                    *pLZ_flags = (mz_uint8)((*pLZ_flags >> 1) | 0x80);

                    s0 = s_tdefl_small_dist_sym[cur_match_dist & 511];
                    s1 = s_tdefl_large_dist_sym[cur_match_dist >> 8];
                    d->m_huff_count[1][(cur_match_dist < 512) ? s0 : s1]++;

                    d->m_huff_count[0][s_tdefl_len_sym[cur_match_len - TDEFL_MIN_MATCH_LEN]]++;
                }
            }
            else
            {
                *pLZ_code_buf++ = (mz_uint8)first_trigram;
                *pLZ_flags = (mz_uint8)(*pLZ_flags >> 1);
                d->m_huff_count[0][(mz_uint8)first_trigram]++;
            }

            if (--num_flags_left == 0)
            {
                num_flags_left = 8;
                pLZ_flags = pLZ_code_buf++;
            }

            total_lz_bytes += cur_match_len;
            lookahead_pos += cur_match_len;
            dict_size = MZ_MIN(dict_size + cur_match_len, (mz_uint)TDEFL_LZ_DICT_SIZE);
            cur_pos = (cur_pos + cur_match_len) & TDEFL_LZ_DICT_SIZE_MASK;
            MZ_ASSERT(lookahead_size >= cur_match_len);
            lookahead_size -= cur_match_len;

            if (pLZ_code_buf > &d->m_lz_code_buf[TDEFL_LZ_CODE_BUF_SIZE - 8])
            {
                int n;
                d->m_lookahead_pos = lookahead_pos;
                d->m_lookahead_size = lookahead_size;
                d->m_dict_size = dict_size;
                d->m_total_lz_bytes = total_lz_bytes;
                d->m_pLZ_code_buf = pLZ_code_buf;
                d->m_pLZ_flags = pLZ_flags;
                d->m_num_flags_left = num_flags_left;
                if ((n = tdefl_flush_block(d, 0)) != 0)
                    return (n < 0) ? MZ_FALSE : MZ_TRUE;
                total_lz_bytes = d->m_total_lz_bytes;
                pLZ_code_buf = d->m_pLZ_code_buf;
                pLZ_flags = d->m_pLZ_flags;
                num_flags_left = d->m_num_flags_left;
            }
        }

        while (lookahead_size)
        {
            mz_uint8 lit = d->m_dict[cur_pos];

            total_lz_bytes++;
            *pLZ_code_buf++ = lit;
            *pLZ_flags = (mz_uint8)(*pLZ_flags >> 1);
            if (--num_flags_left == 0)
            {
                num_flags_left = 8;
                pLZ_flags = pLZ_code_buf++;
            }

            d->m_huff_count[0][lit]++;

            lookahead_pos++;
            dict_size = MZ_MIN(dict_size + 1, (mz_uint)TDEFL_LZ_DICT_SIZE);
            cur_pos = (cur_pos + 1) & TDEFL_LZ_DICT_SIZE_MASK;
            lookahead_size--;

            if (pLZ_code_buf > &d->m_lz_code_buf[TDEFL_LZ_CODE_BUF_SIZE - 8])
            {
                int n;
                d->m_lookahead_pos = lookahead_pos;
                d->m_lookahead_size = lookahead_size;
                d->m_dict_size = dict_size;
                d->m_total_lz_bytes = total_lz_bytes;
                d->m_pLZ_code_buf = pLZ_code_buf;
                d->m_pLZ_flags = pLZ_flags;
                d->m_num_flags_left = num_flags_left;
                if ((n = tdefl_flush_block(d, 0)) != 0)
                    return (n < 0) ? MZ_FALSE : MZ_TRUE;
                total_lz_bytes = d->m_total_lz_bytes;
                pLZ_code_buf = d->m_pLZ_code_buf;
                pLZ_flags = d->m_pLZ_flags;
                num_flags_left = d->m_num_flags_left;
            }
        }
    }

    d->m_lookahead_pos = lookahead_pos;
    d->m_lookahead_size = lookahead_size;
    d->m_dict_size = dict_size;
    d->m_total_lz_bytes = total_lz_bytes;
    d->m_pLZ_code_buf = pLZ_code_buf;
    d->m_pLZ_flags = pLZ_flags;
    d->m_num_flags_left = num_flags_left;
    return MZ_TRUE;
}
#endif /* MINIZ_USE_UNALIGNED_LOADS_AND_STORES && MINIZ_LITTLE_ENDIAN */

static MZ_FORCEINLINE void tdefl_record_literal(tdefl_compressor *d, mz_uint8 lit)
{
    d->m_total_lz_bytes++;
    *d->m_pLZ_code_buf++ = lit;
    *d->m_pLZ_flags = (mz_uint8)(*d->m_pLZ_flags >> 1);
    if (--d->m_num_flags_left == 0)
    {
        d->m_num_flags_left = 8;
        d->m_pLZ_flags = d->m_pLZ_code_buf++;
    }
    d->m_huff_count[0][lit]++;
}

static MZ_FORCEINLINE void tdefl_record_match(tdefl_compressor *d, mz_uint match_len, mz_uint match_dist)
{
    mz_uint32 s0, s1;

    MZ_ASSERT((match_len >= TDEFL_MIN_MATCH_LEN) && (match_dist >= 1) && (match_dist <= TDEFL_LZ_DICT_SIZE));

    d->m_total_lz_bytes += match_len;

    d->m_pLZ_code_buf[0] = (mz_uint8)(match_len - TDEFL_MIN_MATCH_LEN);

    match_dist -= 1;
    d->m_pLZ_code_buf[1] = (mz_uint8)(match_dist & 0xFF);
    d->m_pLZ_code_buf[2] = (mz_uint8)(match_dist >> 8);
    d->m_pLZ_code_buf += 3;

    *d->m_pLZ_flags = (mz_uint8)((*d->m_pLZ_flags >> 1) | 0x80);
    if (--d->m_num_flags_left == 0)
    {
        d->m_num_flags_left = 8;
        d->m_pLZ_flags = d->m_pLZ_code_buf++;
    }

    s0 = s_tdefl_small_dist_sym[match_dist & 511];
    s1 = s_tdefl_large_dist_sym[(match_dist >> 8) & 127];
    d->m_huff_count[1][(match_dist < 512) ? s0 : s1]++;

    if (match_len >= TDEFL_MIN_MATCH_LEN)
        d->m_huff_count[0][s_tdefl_len_sym[match_len - TDEFL_MIN_MATCH_LEN]]++;
}

static mz_bool tdefl_compress_normal(tdefl_compressor *d)
{
    const mz_uint8 *pSrc = d->m_pSrc;
    size_t src_buf_left = d->m_src_buf_left;
    tdefl_flush flush = d->m_flush;

    while ((src_buf_left) || ((flush) && (d->m_lookahead_size)))
    {
        mz_uint len_to_move, cur_match_dist, cur_match_len, cur_pos;
        /* Update dictionary and hash chains. Keeps the lookahead size equal to TDEFL_MAX_MATCH_LEN. */
        if ((d->m_lookahead_size + d->m_dict_size) >= (TDEFL_MIN_MATCH_LEN - 1))
        {
            mz_uint dst_pos = (d->m_lookahead_pos + d->m_lookahead_size) & TDEFL_LZ_DICT_SIZE_MASK, ins_pos = d->m_lookahead_pos + d->m_lookahead_size - 2;
            mz_uint hash = (d->m_dict[ins_pos & TDEFL_LZ_DICT_SIZE_MASK] << TDEFL_LZ_HASH_SHIFT) ^ d->m_dict[(ins_pos + 1) & TDEFL_LZ_DICT_SIZE_MASK];
            mz_uint num_bytes_to_process = (mz_uint)MZ_MIN(src_buf_left, TDEFL_MAX_MATCH_LEN - d->m_lookahead_size);
            const mz_uint8 *pSrc_end = pSrc + num_bytes_to_process;
            src_buf_left -= num_bytes_to_process;
            d->m_lookahead_size += num_bytes_to_process;
            while (pSrc != pSrc_end)
            {
                mz_uint8 c = *pSrc++;
                d->m_dict[dst_pos] = c;
                if (dst_pos < (TDEFL_MAX_MATCH_LEN - 1))
                    d->m_dict[TDEFL_LZ_DICT_SIZE + dst_pos] = c;
                hash = ((hash << TDEFL_LZ_HASH_SHIFT) ^ c) & (TDEFL_LZ_HASH_SIZE - 1);
                d->m_next[ins_pos & TDEFL_LZ_DICT_SIZE_MASK] = d->m_hash[hash];
                d->m_hash[hash] = (mz_uint16)(ins_pos);
                dst_pos = (dst_pos + 1) & TDEFL_LZ_DICT_SIZE_MASK;
                ins_pos++;
            }
        }
        else
        {
            while ((src_buf_left) && (d->m_lookahead_size < TDEFL_MAX_MATCH_LEN))
            {
                mz_uint8 c = *pSrc++;
                mz_uint dst_pos = (d->m_lookahead_pos + d->m_lookahead_size) & TDEFL_LZ_DICT_SIZE_MASK;
                src_buf_left--;
                d->m_dict[dst_pos] = c;
                if (dst_pos < (TDEFL_MAX_MATCH_LEN - 1))
                    d->m_dict[TDEFL_LZ_DICT_SIZE + dst_pos] = c;
                if ((++d->m_lookahead_size + d->m_dict_size) >= TDEFL_MIN_MATCH_LEN)
                {
                    mz_uint ins_pos = d->m_lookahead_pos + (d->m_lookahead_size - 1) - 2;
                    mz_uint hash = ((d->m_dict[ins_pos & TDEFL_LZ_DICT_SIZE_MASK] << (TDEFL_LZ_HASH_SHIFT * 2)) ^ (d->m_dict[(ins_pos + 1) & TDEFL_LZ_DICT_SIZE_MASK] << TDEFL_LZ_HASH_SHIFT) ^ c) & (TDEFL_LZ_HASH_SIZE - 1);
                    d->m_next[ins_pos & TDEFL_LZ_DICT_SIZE_MASK] = d->m_hash[hash];
                    d->m_hash[hash] = (mz_uint16)(ins_pos);
                }
            }
        }
        d->m_dict_size = MZ_MIN(TDEFL_LZ_DICT_SIZE - d->m_lookahead_size, d->m_dict_size);
        if ((!flush) && (d->m_lookahead_size < TDEFL_MAX_MATCH_LEN))
            break;

        /* Simple lazy/greedy parsing state machine. */
        len_to_move = 1;
        cur_match_dist = 0;
        cur_match_len = d->m_saved_match_len ? d->m_saved_match_len : (TDEFL_MIN_MATCH_LEN - 1);
        cur_pos = d->m_lookahead_pos & TDEFL_LZ_DICT_SIZE_MASK;
        if (d->m_flags & (TDEFL_RLE_MATCHES | TDEFL_FORCE_ALL_RAW_BLOCKS))
        {
            if ((d->m_dict_size) && (!(d->m_flags & TDEFL_FORCE_ALL_RAW_BLOCKS)))
            {
                mz_uint8 c = d->m_dict[(cur_pos - 1) & TDEFL_LZ_DICT_SIZE_MASK];
                cur_match_len = 0;
                while (cur_match_len < d->m_lookahead_size)
                {
                    if (d->m_dict[cur_pos + cur_match_len] != c)
                        break;
                    cur_match_len++;
                }
                if (cur_match_len < TDEFL_MIN_MATCH_LEN)
                    cur_match_len = 0;
                else
                    cur_match_dist = 1;
            }
        }
        else
        {
            tdefl_find_match(d, d->m_lookahead_pos, d->m_dict_size, d->m_lookahead_size, &cur_match_dist, &cur_match_len);
        }
        if (((cur_match_len == TDEFL_MIN_MATCH_LEN) && (cur_match_dist >= 8U * 1024U)) || (cur_pos == cur_match_dist) || ((d->m_flags & TDEFL_FILTER_MATCHES) && (cur_match_len <= 5)))
        {
            cur_match_dist = cur_match_len = 0;
        }
        if (d->m_saved_match_len)
        {
            if (cur_match_len > d->m_saved_match_len)
            {
                tdefl_record_literal(d, (mz_uint8)d->m_saved_lit);
                if (cur_match_len >= 128)
                {
                    tdefl_record_match(d, cur_match_len, cur_match_dist);
                    d->m_saved_match_len = 0;
                    len_to_move = cur_match_len;
                }
                else
                {
                    d->m_saved_lit = d->m_dict[cur_pos];
                    d->m_saved_match_dist = cur_match_dist;
                    d->m_saved_match_len = cur_match_len;
                }
            }
            else
            {
                tdefl_record_match(d, d->m_saved_match_len, d->m_saved_match_dist);
                len_to_move = d->m_saved_match_len - 1;
                d->m_saved_match_len = 0;
            }
        }
        else if (!cur_match_dist)
            tdefl_record_literal(d, d->m_dict[MZ_MIN(cur_pos, sizeof(d->m_dict) - 1)]);
        else if ((d->m_greedy_parsing) || (d->m_flags & TDEFL_RLE_MATCHES) || (cur_match_len >= 128))
        {
            tdefl_record_match(d, cur_match_len, cur_match_dist);
            len_to_move = cur_match_len;
        }
        else
        {
            d->m_saved_lit = d->m_dict[MZ_MIN(cur_pos, sizeof(d->m_dict) - 1)];
            d->m_saved_match_dist = cur_match_dist;
            d->m_saved_match_len = cur_match_len;
        }
        /* Move the lookahead forward by len_to_move bytes. */
        d->m_lookahead_pos += len_to_move;
        MZ_ASSERT(d->m_lookahead_size >= len_to_move);
        d->m_lookahead_size -= len_to_move;
        d->m_dict_size = MZ_MIN(d->m_dict_size + len_to_move, (mz_uint)TDEFL_LZ_DICT_SIZE);
        /* Check if it's time to flush the current LZ codes to the internal output buffer. */
        if ((d->m_pLZ_code_buf > &d->m_lz_code_buf[TDEFL_LZ_CODE_BUF_SIZE - 8]) ||
            ((d->m_total_lz_bytes > 31 * 1024) && (((((mz_uint)(d->m_pLZ_code_buf - d->m_lz_code_buf) * 115) >> 7) >= d->m_total_lz_bytes) || (d->m_flags & TDEFL_FORCE_ALL_RAW_BLOCKS))))
        {
            int n;
            d->m_pSrc = pSrc;
            d->m_src_buf_left = src_buf_left;
            if ((n = tdefl_flush_block(d, 0)) != 0)
                return (n < 0) ? MZ_FALSE : MZ_TRUE;
        }
    }

    d->m_pSrc = pSrc;
    d->m_src_buf_left = src_buf_left;
    return MZ_TRUE;
}

static tdefl_status tdefl_flush_output_buffer(tdefl_compressor *d)
{
    if (d->m_pIn_buf_size)
    {
        *d->m_pIn_buf_size = d->m_pSrc - (const mz_uint8 *)d->m_pIn_buf;
    }

    if (d->m_pOut_buf_size)
    {
        size_t n = MZ_MIN(*d->m_pOut_buf_size - d->m_out_buf_ofs, d->m_output_flush_remaining);
        memcpy((mz_uint8 *)d->m_pOut_buf + d->m_out_buf_ofs, d->m_output_buf + d->m_output_flush_ofs, n);
        d->m_output_flush_ofs += (mz_uint)n;
        d->m_output_flush_remaining -= (mz_uint)n;
        d->m_out_buf_ofs += n;

        *d->m_pOut_buf_size = d->m_out_buf_ofs;
    }

    return (d->m_finished && !d->m_output_flush_remaining) ? TDEFL_STATUS_DONE : TDEFL_STATUS_OKAY;
}

tdefl_status tdefl_compress(tdefl_compressor *d, const void *pIn_buf, size_t *pIn_buf_size, void *pOut_buf, size_t *pOut_buf_size, tdefl_flush flush)
{
    if (!d)
    {
        if (pIn_buf_size)
            *pIn_buf_size = 0;
        if (pOut_buf_size)
            *pOut_buf_size = 0;
        return TDEFL_STATUS_BAD_PARAM;
    }

    d->m_pIn_buf = pIn_buf;
    d->m_pIn_buf_size = pIn_buf_size;
    d->m_pOut_buf = pOut_buf;
    d->m_pOut_buf_size = pOut_buf_size;
    d->m_pSrc = (const mz_uint8 *)(pIn_buf);
    d->m_src_buf_left = pIn_buf_size ? *pIn_buf_size : 0;
    d->m_out_buf_ofs = 0;
    d->m_flush = flush;

    if (((d->m_pPut_buf_func != NULL) == ((pOut_buf != NULL) || (pOut_buf_size != NULL))) || (d->m_prev_return_status != TDEFL_STATUS_OKAY) ||
        (d->m_wants_to_finish && (flush != TDEFL_FINISH)) || (pIn_buf_size && *pIn_buf_size && !pIn_buf) || (pOut_buf_size && *pOut_buf_size && !pOut_buf))
    {
        if (pIn_buf_size)
            *pIn_buf_size = 0;
        if (pOut_buf_size)
            *pOut_buf_size = 0;
        return (d->m_prev_return_status = TDEFL_STATUS_BAD_PARAM);
    }
    d->m_wants_to_finish |= (flush == TDEFL_FINISH);

    if ((d->m_output_flush_remaining) || (d->m_finished))
        return (d->m_prev_return_status = tdefl_flush_output_buffer(d));

#if MINIZ_USE_UNALIGNED_LOADS_AND_STORES && MINIZ_LITTLE_ENDIAN
    if (((d->m_flags & TDEFL_MAX_PROBES_MASK) == 1) &&
        ((d->m_flags & TDEFL_GREEDY_PARSING_FLAG) != 0) &&
        ((d->m_flags & (TDEFL_FILTER_MATCHES | TDEFL_FORCE_ALL_RAW_BLOCKS | TDEFL_RLE_MATCHES)) == 0))
    {
        if (!tdefl_compress_fast(d))
            return d->m_prev_return_status;
    }
    else
#endif /* #if MINIZ_USE_UNALIGNED_LOADS_AND_STORES && MINIZ_LITTLE_ENDIAN */
    {
        if (!tdefl_compress_normal(d))
            return d->m_prev_return_status;
    }

    if ((d->m_flags & (TDEFL_WRITE_ZLIB_HEADER | TDEFL_COMPUTE_ADLER32)) && (pIn_buf))
        d->m_adler32 = (mz_uint32)mz_adler32(d->m_adler32, (const mz_uint8 *)pIn_buf, d->m_pSrc - (const mz_uint8 *)pIn_buf);

    if ((flush) && (!d->m_lookahead_size) && (!d->m_src_buf_left) && (!d->m_output_flush_remaining))
    {
        if (tdefl_flush_block(d, flush) < 0)
            return d->m_prev_return_status;
        d->m_finished = (flush == TDEFL_FINISH);
        if (flush == TDEFL_FULL_FLUSH)
        {
            MZ_CLEAR_OBJ(d->m_hash);
            MZ_CLEAR_OBJ(d->m_next);
            d->m_dict_size = 0;
        }
    }

    return (d->m_prev_return_status = tdefl_flush_output_buffer(d));
}

tdefl_status tdefl_compress_buffer(tdefl_compressor *d, const void *pIn_buf, size_t in_buf_size, tdefl_flush flush)
{
    MZ_ASSERT(d->m_pPut_buf_func);
    return tdefl_compress(d, pIn_buf, &in_buf_size, NULL, NULL, flush);
}

tdefl_status tdefl_init(tdefl_compressor *d, tdefl_put_buf_func_ptr pPut_buf_func, void *pPut_buf_user, int flags)
{
    d->m_pPut_buf_func = pPut_buf_func;
    d->m_pPut_buf_user = pPut_buf_user;
    d->m_flags = (mz_uint)(flags);
    d->m_max_probes[0] = 1 + ((flags & 0xFFF) + 2) / 3;
    d->m_greedy_parsing = (flags & TDEFL_GREEDY_PARSING_FLAG) != 0;
    d->m_max_probes[1] = 1 + (((flags & 0xFFF) >> 2) + 2) / 3;
    if (!(flags & TDEFL_NONDETERMINISTIC_PARSING_FLAG))
        MZ_CLEAR_OBJ(d->m_hash);
    d->m_lookahead_pos = d->m_lookahead_size = d->m_dict_size = d->m_total_lz_bytes = d->m_lz_code_buf_dict_pos = d->m_bits_in = 0;
    d->m_output_flush_ofs = d->m_output_flush_remaining = d->m_finished = d->m_block_index = d->m_bit_buffer = d->m_wants_to_finish = 0;
    d->m_pLZ_code_buf = d->m_lz_code_buf + 1;
    d->m_pLZ_flags = d->m_lz_code_buf;
    d->m_num_flags_left = 8;
    d->m_pOutput_buf = d->m_output_buf;
    d->m_pOutput_buf_end = d->m_output_buf;
    d->m_prev_return_status = TDEFL_STATUS_OKAY;
    d->m_saved_match_dist = d->m_saved_match_len = d->m_saved_lit = 0;
    d->m_adler32 = 1;
    d->m_pIn_buf = NULL;
    d->m_pOut_buf = NULL;
    d->m_pIn_buf_size = NULL;
    d->m_pOut_buf_size = NULL;
    d->m_flush = TDEFL_NO_FLUSH;
    d->m_pSrc = NULL;
    d->m_src_buf_left = 0;
    d->m_out_buf_ofs = 0;
    if (!(flags & TDEFL_NONDETERMINISTIC_PARSING_FLAG))
        MZ_CLEAR_OBJ(d->m_dict);
    memset(&d->m_huff_count[0][0], 0, sizeof(d->m_huff_count[0][0]) * TDEFL_MAX_HUFF_SYMBOLS_0);
    memset(&d->m_huff_count[1][0], 0, sizeof(d->m_huff_count[1][0]) * TDEFL_MAX_HUFF_SYMBOLS_1);
    return TDEFL_STATUS_OKAY;
}

tdefl_status tdefl_get_prev_return_status(tdefl_compressor *d)
{
    return d->m_prev_return_status;
}

mz_uint32 tdefl_get_adler32(tdefl_compressor *d)
{
    return d->m_adler32;
}

mz_bool tdefl_compress_mem_to_output(const void *pBuf, size_t buf_len, tdefl_put_buf_func_ptr pPut_buf_func, void *pPut_buf_user, int flags)
{
    tdefl_compressor *pComp;
    mz_bool succeeded;
    if (((buf_len) && (!pBuf)) || (!pPut_buf_func))
        return MZ_FALSE;
    pComp = (tdefl_compressor *)MZ_MALLOC(sizeof(tdefl_compressor));
    if (!pComp)
        return MZ_FALSE;
    succeeded = (tdefl_init(pComp, pPut_buf_func, pPut_buf_user, flags) == TDEFL_STATUS_OKAY);
    succeeded = succeeded && (tdefl_compress_buffer(pComp, pBuf, buf_len, TDEFL_FINISH) == TDEFL_STATUS_DONE);
    MZ_FREE(pComp);
    return succeeded;
}

typedef struct
{
    size_t m_size, m_capacity;
    mz_uint8 *m_pBuf;
    mz_bool m_expandable;
} tdefl_output_buffer;

static mz_bool tdefl_output_buffer_putter(const void *pBuf, int len, void *pUser)
{
    tdefl_output_buffer *p = (tdefl_output_buffer *)pUser;
    size_t new_size = p->m_size + len;
    if (new_size > p->m_capacity)
    {
        size_t new_capacity = p->m_capacity;
        mz_uint8 *pNew_buf;
        if (!p->m_expandable)
            return MZ_FALSE;
        do
        {
            new_capacity = MZ_MAX(128U, new_capacity << 1U);
        } while (new_size > new_capacity);
        pNew_buf = (mz_uint8 *)MZ_REALLOC(p->m_pBuf, new_capacity);
        if (!pNew_buf)
            return MZ_FALSE;
        p->m_pBuf = pNew_buf;
        p->m_capacity = new_capacity;
    }
    memcpy((mz_uint8 *)p->m_pBuf + p->m_size, pBuf, len);
    p->m_size = new_size;
    return MZ_TRUE;
}

void *tdefl_compress_mem_to_heap(const void *pSrc_buf, size_t src_buf_len, size_t *pOut_len, int flags)
{
    tdefl_output_buffer out_buf;
    MZ_CLEAR_OBJ(out_buf);
    if (!pOut_len)
        return MZ_FALSE;
    else
        *pOut_len = 0;
    out_buf.m_expandable = MZ_TRUE;
    if (!tdefl_compress_mem_to_output(pSrc_buf, src_buf_len, tdefl_output_buffer_putter, &out_buf, flags))
        return NULL;
    *pOut_len = out_buf.m_size;
    return out_buf.m_pBuf;
}

size_t tdefl_compress_mem_to_mem(void *pOut_buf, size_t out_buf_len, const void *pSrc_buf, size_t src_buf_len, int flags)
{
    tdefl_output_buffer out_buf;
    MZ_CLEAR_OBJ(out_buf);
    if (!pOut_buf)
        return 0;
    out_buf.m_pBuf = (mz_uint8 *)pOut_buf;
    out_buf.m_capacity = out_buf_len;
    if (!tdefl_compress_mem_to_output(pSrc_buf, src_buf_len, tdefl_output_buffer_putter, &out_buf, flags))
        return 0;
    return out_buf.m_size;
}

static const mz_uint s_tdefl_num_probes[11] = { 0, 1, 6, 32, 16, 32, 128, 256, 512, 768, 1500 };

/* level may actually range from [0,10] (10 is a "hidden" max level, where we want a bit more compression and it's fine if throughput to fall off a cliff on some files). */
mz_uint tdefl_create_comp_flags_from_zip_params(int level, int window_bits, int strategy)
{
    mz_uint comp_flags = s_tdefl_num_probes[(level >= 0) ? MZ_MIN(10, level) : MZ_DEFAULT_LEVEL] | ((level <= 3) ? TDEFL_GREEDY_PARSING_FLAG : 0);
    if (window_bits > 0)
        comp_flags |= TDEFL_WRITE_ZLIB_HEADER;

    if (!level)
        comp_flags |= TDEFL_FORCE_ALL_RAW_BLOCKS;
    else if (strategy == MZ_FILTERED)
        comp_flags |= TDEFL_FILTER_MATCHES;
    else if (strategy == MZ_HUFFMAN_ONLY)
        comp_flags &= ~TDEFL_MAX_PROBES_MASK;
    else if (strategy == MZ_FIXED)
        comp_flags |= TDEFL_FORCE_ALL_STATIC_BLOCKS;
    else if (strategy == MZ_RLE)
        comp_flags |= TDEFL_RLE_MATCHES;

    return comp_flags;
}

#ifdef _MSC_VER
#pragma warning(push)
#pragma warning(disable : 4204) /* nonstandard extension used : non-constant aggregate initializer (also supported by GNU C and C99, so no big deal) */
#endif
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
