666zhaobo666/HoloCubic/AIO_Tool/esptool_v41/flasher_stub/stub_flasher.c

/*
 * SPDX-FileCopyrightText: 2016 Cesanta Software Limited
 *
 * SPDX-License-Identifier: GPL-2.0-or-later
 *
 * SPDX-FileContributor: 2016-2022 Espressif Systems (Shanghai) CO LTD
 */

/*
 * Main flasher stub logic
 *
 * This stub uses the same SLIP framing and basic command/response structure
 * as the in-ROM flasher program, but with some enhanced
 * functions and also standardizes the flasher features between different chips.
 *
 * Actual command handlers are implemented in stub_commands.c
 */
#include <stdlib.h>
#include "stub_flasher.h"
#include "rom_functions.h"
#include "slip.h"
#include "stub_commands.h"
#include "stub_write_flash.h"
#include "stub_io.h"
#include "soc_support.h"

/* Buffers for reading from UART. Data is read double-buffered, so
   we can read into one buffer while handling data from the other one
   (used for flashing throughput.) */
typedef struct {
  uint8_t buf_a[MAX_WRITE_BLOCK+64];
  uint8_t buf_b[MAX_WRITE_BLOCK+64];
  volatile uint8_t *reading_buf; /* Pointer to buf_a, or buf_b - which are we reading_buf? */
  uint16_t read; /* how many bytes have we read in the frame */
  slip_state_t state;
  esp_command_req_t *command; /* Pointer to buf_a or buf_b as latest command received */
} uart_buf_t;
static volatile uart_buf_t ub;

/* esptool protcol "checksum" is XOR of 0xef and each byte of
   data payload. */
static uint8_t calculate_checksum(uint8_t *buf, int length)
{
  uint8_t res = 0xef;
  for(int i = 0; i < length; i++) {
    res ^= buf[i];
  }
  return res;
}

static void stub_handle_rx_byte(char byte)
{
  int16_t r = SLIP_recv_byte(byte, (slip_state_t *)&ub.state);
  if (r >= 0) {
    ub.reading_buf[ub.read++] = (uint8_t) r;
    if (ub.read == MAX_WRITE_BLOCK+64) {
      /* shouldn't happen unless there are data errors */
      r = SLIP_FINISHED_FRAME;
    }
  }
  if (r == SLIP_FINISHED_FRAME) {
    /* end of frame, set 'command'
       to be processed by main thread */
    if(ub.reading_buf == ub.buf_a) {
      ub.command = (esp_command_req_t *)ub.buf_a;
      ub.reading_buf = ub.buf_b;
    } else {
      ub.command = (esp_command_req_t *)ub.buf_b;
      ub.reading_buf = ub.buf_a;
    }
    ub.read = 0;
  }
}

static esp_command_error verify_data_len(esp_command_req_t *command, uint8_t len)
{
  return (command->data_len == len) ? ESP_OK : ESP_BAD_DATA_LEN;
}
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
